shreekumar3d/jigita/demo/wip/smd/tssop20-breakout/scan-helper.FCStd

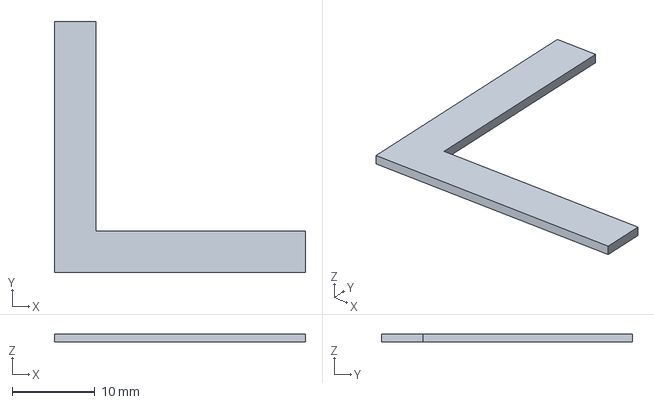
[picture p30: CAD file, 2025-02-22]
demo/wip/smd/tssop20-breakout/scan-helper.FCStd
30.4 x 30.4 x 1.00 mm
