shreekumar3d/jigita/test-boards/component-orientation-test/3dmodels/ssd1306-yrot135.step

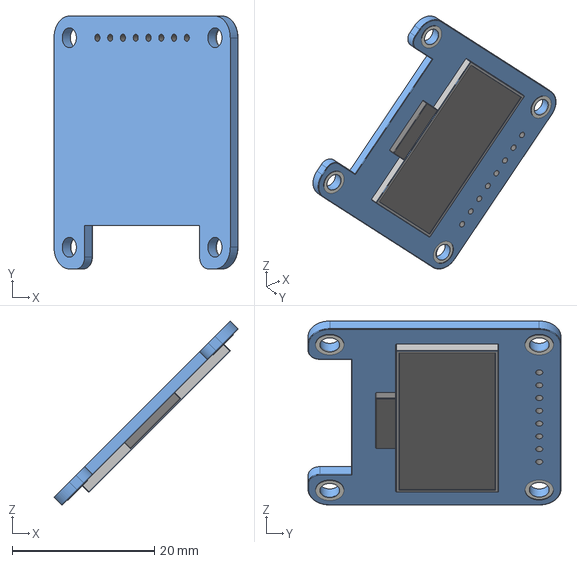
[picture p31: CAD file, 2024-11-05]
test-boards/component-orientation-test/3dmodels/ssd1306-yrot135.step
25.9 x 35.6 x 25.9 mm
