shreekumar3d/jigita/test-boards/footprint-test/2x20pin_berg_header.stl

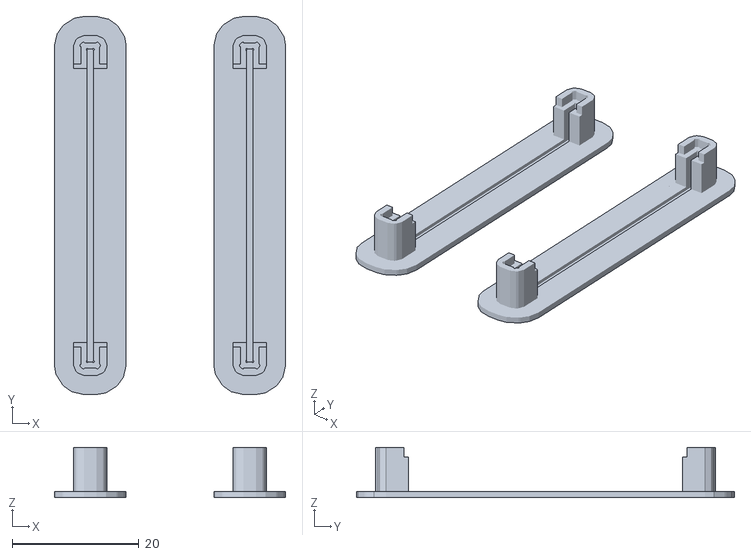
[picture p32: CAD file, 2025-02-27]
test-boards/footprint-test/2x20pin_berg_header.stl
36.5 x 59.6 x 7.94
