shreekumar3d/jigita/test-boards/hello/gen/hello-jig.stl

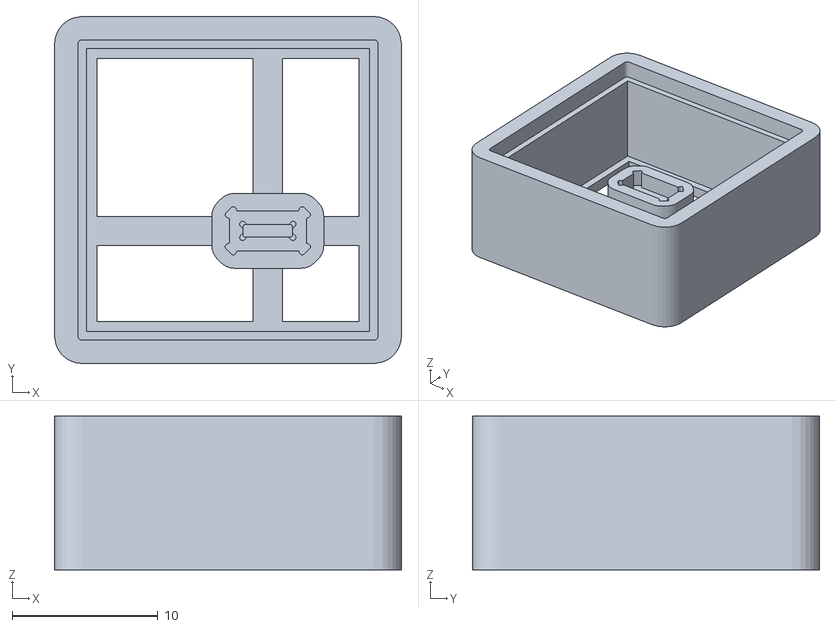
[picture p33: CAD file, 2025-03-18]
test-boards/hello/gen/hello-jig.stl
23.8 x 23.8 x 10.5
