shreekumar3d/jigita/demo/01-rpi-pico-soldering-jig/jigs/pico-soldering-jig.3mf

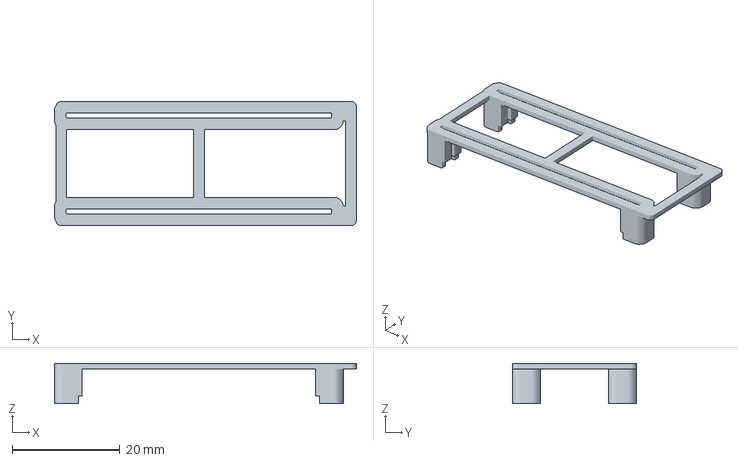
[picture p34: CAD file, 2025-03-20]
demo/01-rpi-pico-soldering-jig/jigs/pico-soldering-jig.3mf
55.9 x 23.0 x 7.44 mm
