shreekumar3d/jigita/demo/03-fossdem-audio-board/jigs/mixolydian-4x4-soldering-jig-solid.3mf

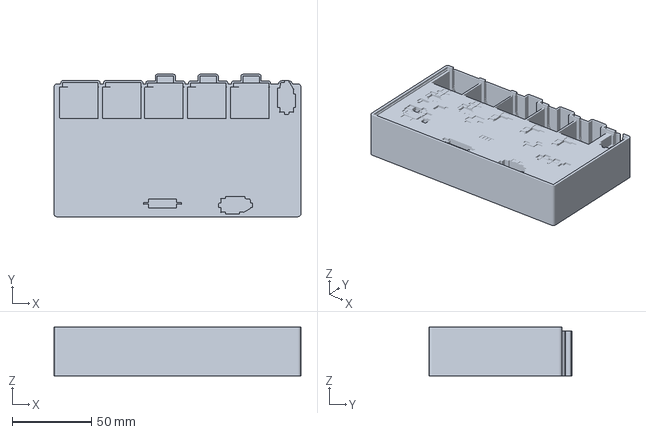
[picture p35: CAD file, 2025-03-24]
demo/03-fossdem-audio-board/jigs/mixolydian-4x4-soldering-jig-solid.3mf
155.8 x 89.9 x 30.8 mm
