shreekumar3d/jigita/demo/04-ativega/jigs/ativega-jig.3mf

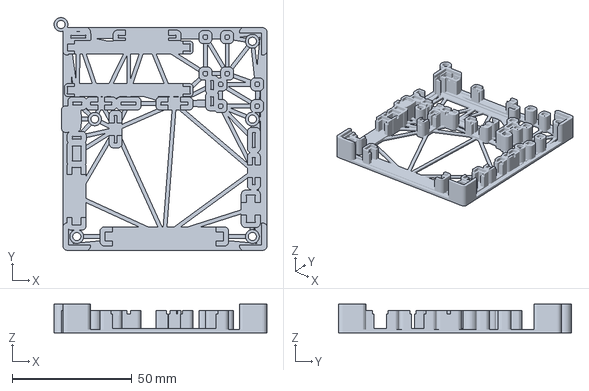
[picture p36: CAD file, 2025-03-26]
demo/04-ativega/jigs/ativega-jig.3mf
88.9 x 97.2 x 11.9 mm
