shreekumar3d/jigita/demo/05-gridfinity/allen-keys/3dmodels/2-HexKey.step

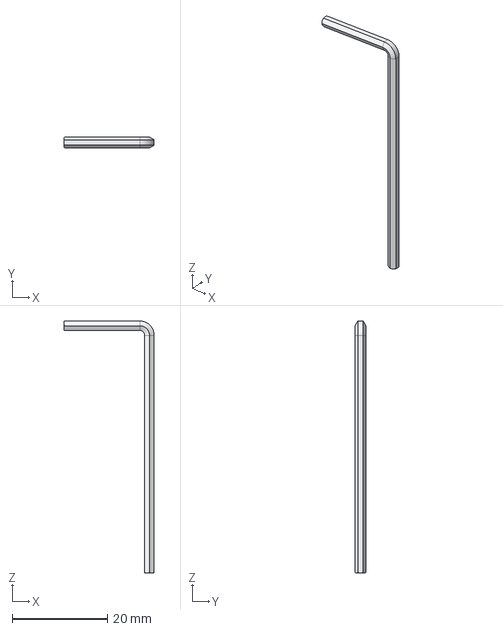
[picture p37: CAD file, 2025-03-27]
demo/05-gridfinity/allen-keys/3dmodels/2-HexKey.step
19.0 x 2.31 x 53.0 mm
