shreekumar3d/jigita/demo/05-gridfinity/base/base-gridfinity-1x1.stl

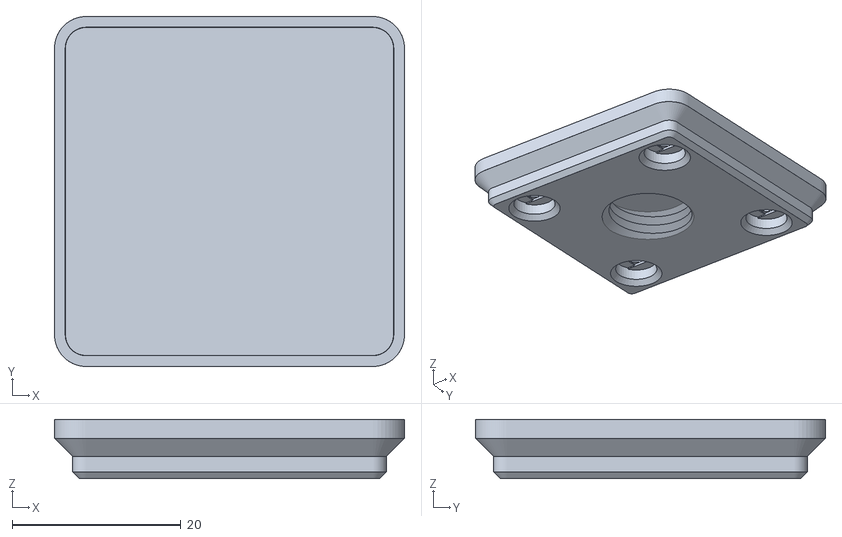
[picture p38: CAD file, 2025-03-26]
demo/05-gridfinity/base/base-gridfinity-1x1.stl
41.5 x 41.5 x 7.00
