shreekumar3d/jigita/demo/05-gridfinity/containers/gridfinity-container-8x10pin-header.stl

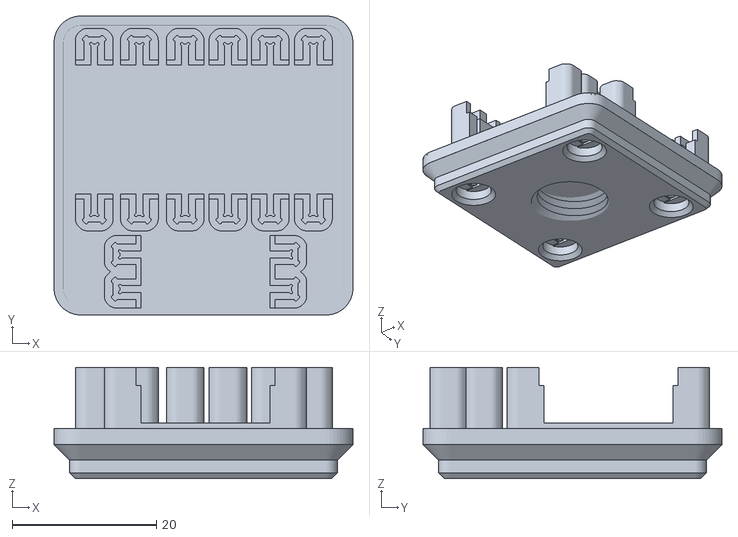
[picture p39: CAD file, 2025-03-26]
demo/05-gridfinity/containers/gridfinity-container-8x10pin-header.stl
41.5 x 41.5 x 15.5
