shreekumar3d/jigita/demo/05-gridfinity/fitting/gridfinity-1x1.FCStd

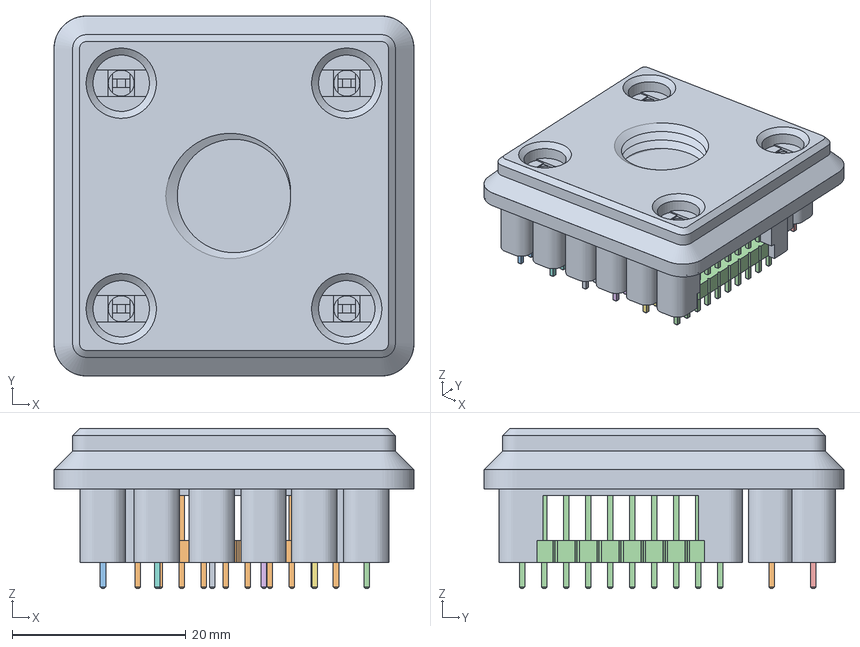
[picture p40: CAD file, 2025-03-26]
demo/05-gridfinity/fitting/gridfinity-1x1.FCStd
41.5 x 41.5 x 18.5 mm
PinHeader_1x10_P254mm_Vertical
PinHeader_1x10_P254mm_Vertical001
PinHeader_1x10_P254mm_Vertical002
PinHeader_1x10_P254mm_Vertical003
PinHeader_1x10_P254mm_Vertical004
PinHeader_1x10_P254mm_Vertical005
PinHeader_1x10_P254mm_Vertical006
PinHeader_1x10_P254mm_Vertical007
gridfinity-container-8x10pin-header
