shreekumar3d/jigita/demo/05-gridfinity/jigs/gridfinity-1x1.3mf

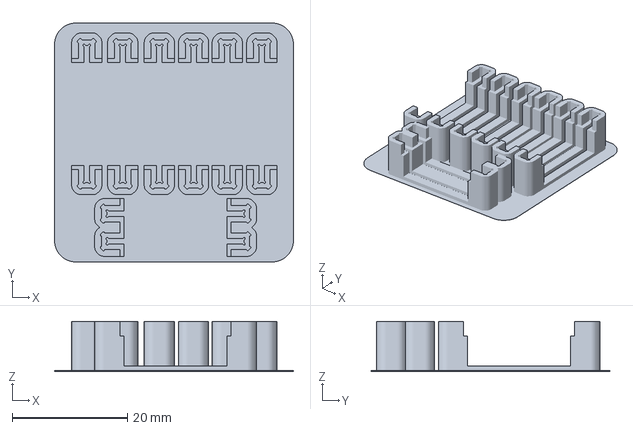
[picture p41: CAD file, 2025-03-26]
demo/05-gridfinity/jigs/gridfinity-1x1.3mf
41.5 x 41.5 x 8.74 mm
