shreekumar3d/jigita/test-boards/component-orientation-test/3dmodels/ssd1306-xrot90.step

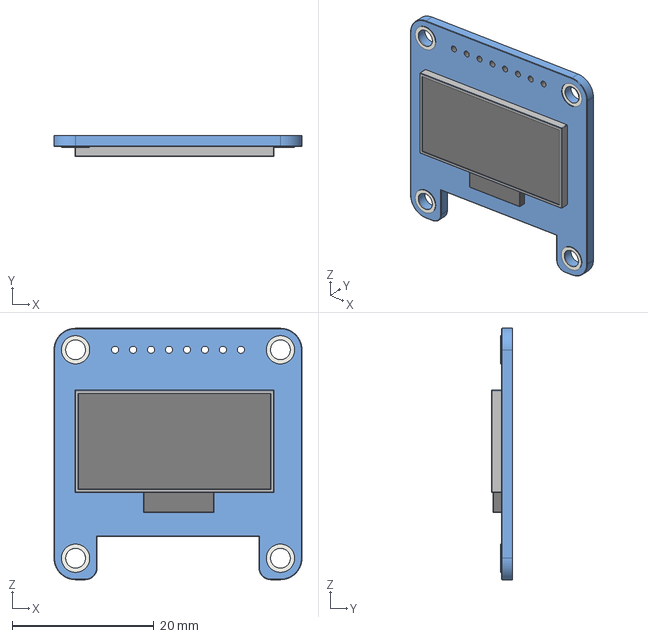
[picture p42: CAD file, 2024-11-05]
test-boards/component-orientation-test/3dmodels/ssd1306-xrot90.step
35.1 x 3.00 x 35.6 mm
