shreekumar3d/jigita/test-boards/hello/gen/hello-kicad.step

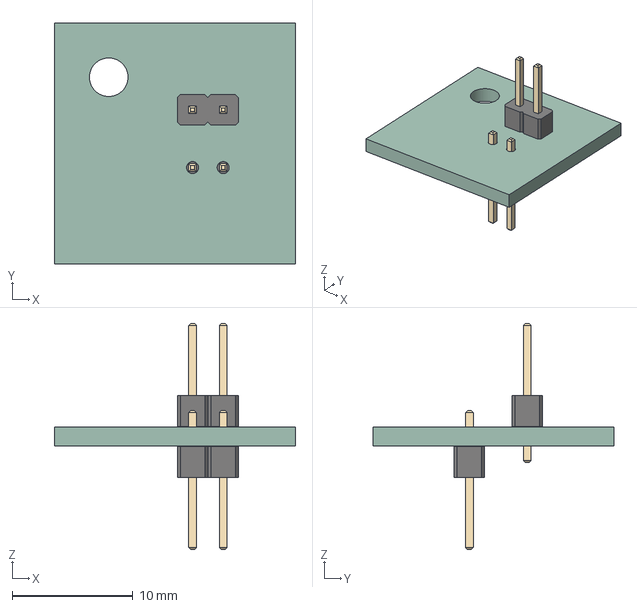
[picture p43: CAD file, 2025-03-18]
test-boards/hello/gen/hello-kicad.step
20.0 x 20.0 x 18.8 mm
PinHeader_1x02_P254mm_Vertical x 2
hello_PCB
