shreekumar3d/jigita/demo/01-rpi-pico-soldering-jig/jigs/pico-all-soldering-jig.3mf

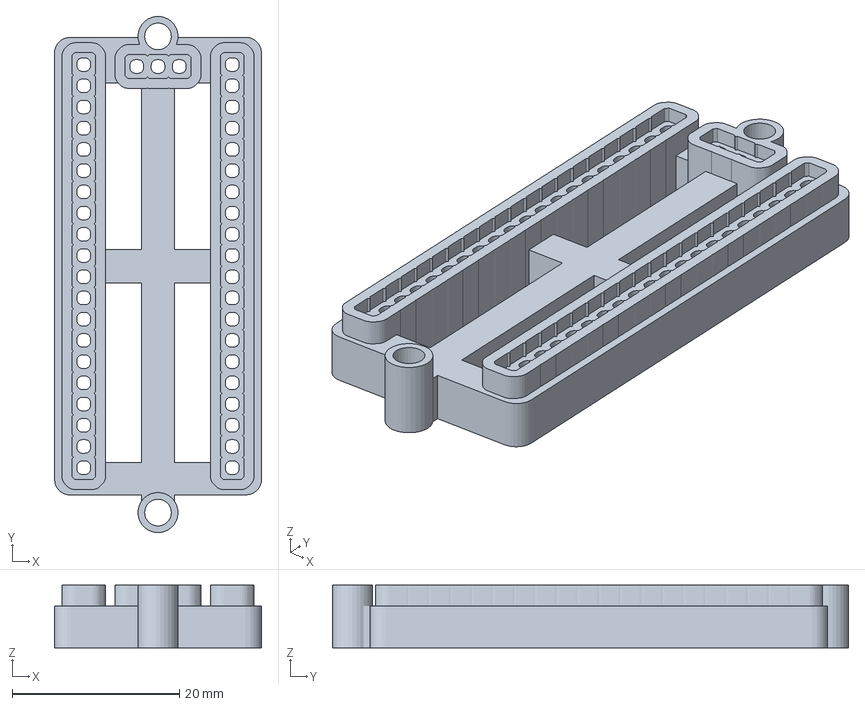
[picture p44: CAD file, 2025-03-20]
demo/01-rpi-pico-soldering-jig/jigs/pico-all-soldering-jig.3mf
24.8 x 61.8 x 7.54 mm
