shreekumar3d/jigita/demo/05-gridfinity/allen-keys/3dmodels/3-HexKey.step

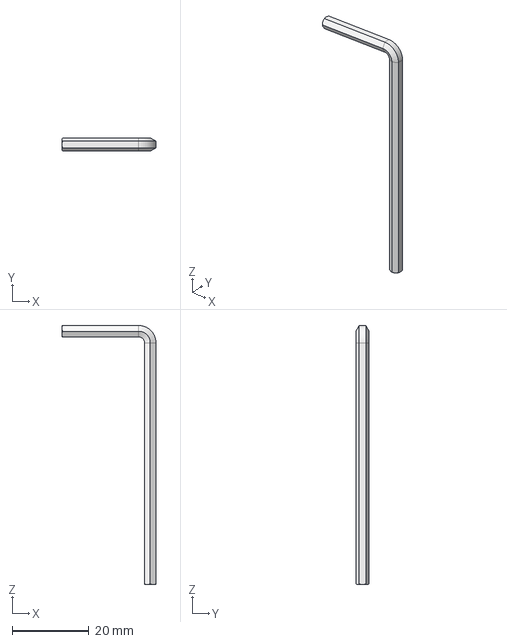
[picture p45: CAD file, 2025-03-27]
demo/05-gridfinity/allen-keys/3dmodels/3-HexKey.step
24.5 x 3.46 x 67.5 mm
