shreekumar3d/jigita/test-boards/component-orientation-test/3dmodels/ssd1306-zrot135.step

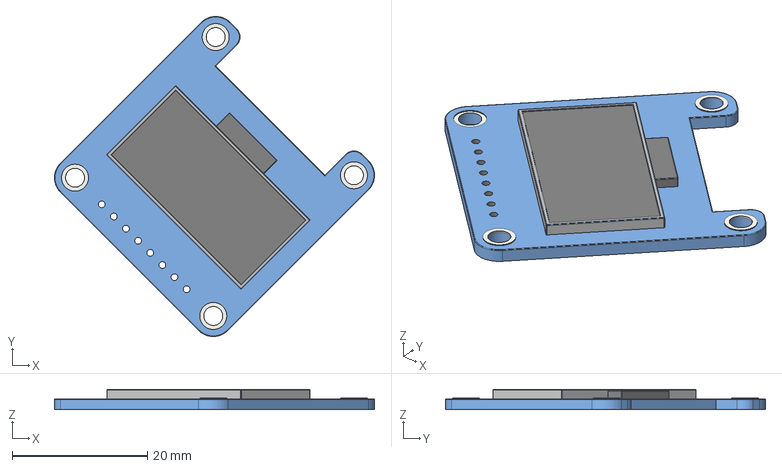
[picture p46: CAD file, 2024-11-05]
test-boards/component-orientation-test/3dmodels/ssd1306-zrot135.step
47.4 x 47.4 x 3.00 mm
