shreekumar3d/jigita/test-boards/hello/gen/hello-jig-on-board.FCStd

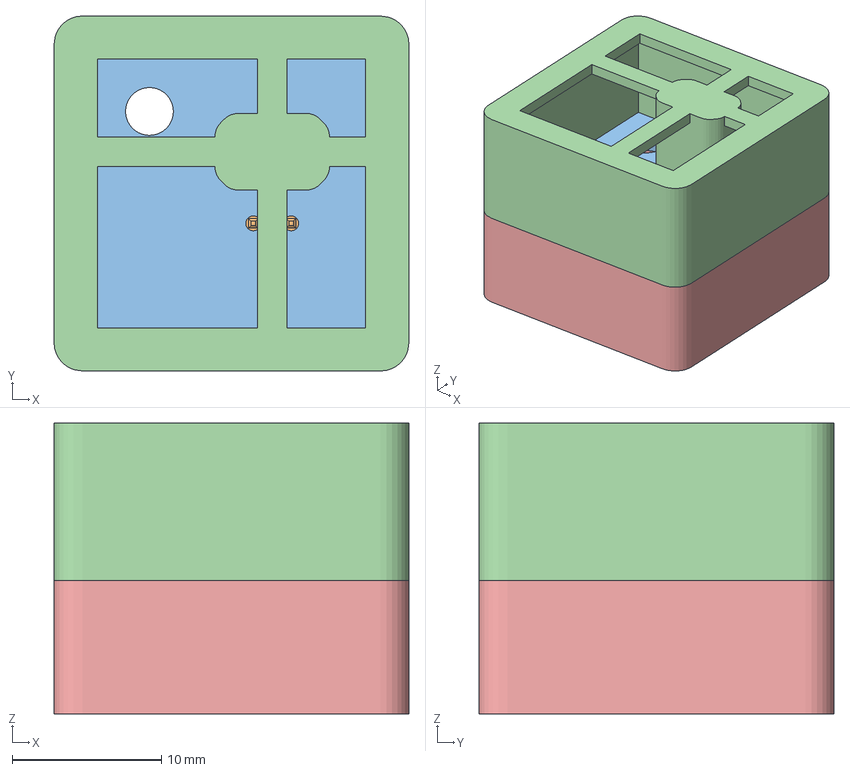
[picture p47: CAD file, 2025-03-18]
test-boards/hello/gen/hello-jig-on-board.FCStd
23.8 x 23.8 x 19.5 mm
PinHeader_1x02_P254mm_Vertical
PinHeader_1x02_P254mm_Vertical001
hello_PCB
hello-jig-step-coord
hello-jig-bottom-step-coord
