shreekumar3d/jigita/test-boards/footprint-test/kicad_single_row_headers.scad

// Customizable Jig Generator
// In OpenSCAD, use "Description Only" for best user experience
// understanding the tunable parameters.
// -----------------------------------------------------
// Auto generated file by jigit, the awesome automatic
// jig generator for your PCB designs. Checkout the project
// at https://github.com/shreekumar3d/jigit
// -----------------------------------------------------
// Configuration file : config.toml
//
// Complete configuration file is embedded at the end of this
// file.
//Thickness(height) of base
Base_Thickness = 0.4; // [0.0:0.2:1.0]
/* [Include these footprints in output STL file] */
//Connector_PinHeader_2.54mm:PinHeader_1x01_P2.54mm_Vertical
Include_FP1_in_Jig=true; // [false,true]
//Connector_PinHeader_2.54mm:PinHeader_1x02_P2.54mm_Vertical
Include_FP2_in_Jig=true; // [false,true]
//Connector_PinHeader_2.54mm:PinHeader_1x03_P2.54mm_Vertical
Include_FP3_in_Jig=true; // [false,true]
//Connector_PinHeader_2.54mm:PinHeader_1x04_P2.54mm_Vertical
Include_FP4_in_Jig=true; // [false,true]
//Connector_PinHeader_2.54mm:PinHeader_1x05_P2.54mm_Vertical
Include_FP5_in_Jig=true; // [false,true]
//Connector_PinHeader_2.54mm:PinHeader_1x06_P2.54mm_Vertical
Include_FP6_in_Jig=true; // [false,true]
//Connector_PinHeader_2.54mm:PinHeader_1x07_P2.54mm_Vertical
Include_FP7_in_Jig=true; // [false,true]
//Connector_PinHeader_2.54mm:PinHeader_1x08_P2.54mm_Vertical
Include_FP8_in_Jig=true; // [false,true]
//Connector_PinHeader_2.54mm:PinHeader_1x09_P2.54mm_Vertical
Include_FP9_in_Jig=true; // [false,true]
/* [Footprint: Connector_PinHeader_2.54mm:PinHeader_1x01_P2.54mm_Vertical] */
//XY Gap in shell for component insertion
Effective_Shell_Gap_For_FP1 = 0.1;
//Thickness of shell
Effective_Shell_Thickness_For_FP1 = 1.2;
//Z distance from start of shell to PCB
Effective_Shell_Clearance_From_PCB_For_FP1 = 1;
//Type of shell for this footprint
Shell_Type_For_FP1="fitting"; // [wiggle,fitting,fitting_flower,tight,courtyard]
//Insert this component into jig from this side.(Bottom insertion requires wiggle or courtyard shell to work)
Insert_FP1_From="top"; // [top,bottom]
//Wrapper thickness
Wrapper_Thickness_For_FP1=0.0; // [0:0.1:10.0]
//Wrapper height
Wrapper_Height_For_FP1=0.0; // [0:0.1:8.539479970932007]
/* [Footprint: Connector_PinHeader_2.54mm:PinHeader_1x02_P2.54mm_Vertical] */
//XY Gap in shell for component insertion
Effective_Shell_Gap_For_FP2 = 0.1;
//Thickness of shell
Effective_Shell_Thickness_For_FP2 = 1.2;
//Z distance from start of shell to PCB
Effective_Shell_Clearance_From_PCB_For_FP2 = 1;
//Type of shell for this footprint
Shell_Type_For_FP2="fitting"; // [wiggle,fitting,fitting_flower,tight,courtyard]
//Insert this component into jig from this side.(Bottom insertion requires wiggle or courtyard shell to work)
Insert_FP2_From="top"; // [top,bottom]
//Wrapper thickness
Wrapper_Thickness_For_FP2=0.0; // [0:0.1:10.0]
//Wrapper height
Wrapper_Height_For_FP2=0.0; // [0:0.1:8.539479970932007]
/* [Footprint: Connector_PinHeader_2.54mm:PinHeader_1x03_P2.54mm_Vertical] */
//XY Gap in shell for component insertion
Effective_Shell_Gap_For_FP3 = 0.1;
//Thickness of shell
Effective_Shell_Thickness_For_FP3 = 1.2;
//Z distance from start of shell to PCB
Effective_Shell_Clearance_From_PCB_For_FP3 = 1;
//Type of shell for this footprint
Shell_Type_For_FP3="fitting"; // [wiggle,fitting,fitting_flower,tight,courtyard]
//Insert this component into jig from this side.(Bottom insertion requires wiggle or courtyard shell to work)
Insert_FP3_From="top"; // [top,bottom]
//Wrapper thickness
Wrapper_Thickness_For_FP3=0.0; // [0:0.1:10.0]
//Wrapper height
Wrapper_Height_For_FP3=0.0; // [0:0.1:8.539479970932007]
/* [Footprint: Connector_PinHeader_2.54mm:PinHeader_1x04_P2.54mm_Vertical] */
//XY Gap in shell for component insertion
Effective_Shell_Gap_For_FP4 = 0.1;
//Thickness of shell
Effective_Shell_Thickness_For_FP4 = 1.2;
//Z distance from start of shell to PCB
Effective_Shell_Clearance_From_PCB_For_FP4 = 1;
//Type of shell for this footprint
Shell_Type_For_FP4="fitting"; // [wiggle,fitting,fitting_flower,tight,courtyard]
//Insert this component into jig from this side.(Bottom insertion requires wiggle or courtyard shell to work)
Insert_FP4_From="top"; // [top,bottom]
//Wrapper thickness
Wrapper_Thickness_For_FP4=0.0; // [0:0.1:10.0]
//Wrapper height
Wrapper_Height_For_FP4=0.0; // [0:0.1:8.539479970932007]
/* [Footprint: Connector_PinHeader_2.54mm:PinHeader_1x05_P2.54mm_Vertical] */
//XY Gap in shell for component insertion
Effective_Shell_Gap_For_FP5 = 0.1;
//Thickness of shell
Effective_Shell_Thickness_For_FP5 = 1.2;
//Z distance from start of shell to PCB
Effective_Shell_Clearance_From_PCB_For_FP5 = 1;
//Type of shell for this footprint
Shell_Type_For_FP5="fitting"; // [wiggle,fitting,fitting_flower,tight,courtyard]
//Insert this component into jig from this side.(Bottom insertion requires wiggle or courtyard shell to work)
Insert_FP5_From="top"; // [top,bottom]
//Wrapper thickness
Wrapper_Thickness_For_FP5=0.0; // [0:0.1:10.0]
//Wrapper height
Wrapper_Height_For_FP5=0.0; // [0:0.1:8.539479970932007]
/* [Footprint: Connector_PinHeader_2.54mm:PinHeader_1x06_P2.54mm_Vertical] */
//XY Gap in shell for component insertion
Effective_Shell_Gap_For_FP6 = 0.1;
//Thickness of shell
Effective_Shell_Thickness_For_FP6 = 1.2;
//Z distance from start of shell to PCB
Effective_Shell_Clearance_From_PCB_For_FP6 = 1;
//Type of shell for this footprint
Shell_Type_For_FP6="fitting"; // [wiggle,fitting,fitting_flower,tight,courtyard]
//Insert this component into jig from this side.(Bottom insertion requires wiggle or courtyard shell to work)
Insert_FP6_From="top"; // [top,bottom]
//Wrapper thickness
Wrapper_Thickness_For_FP6=0.0; // [0:0.1:10.0]
//Wrapper height
Wrapper_Height_For_FP6=0.0; // [0:0.1:8.539479970932007]
/* [Footprint: Connector_PinHeader_2.54mm:PinHeader_1x07_P2.54mm_Vertical] */
//XY Gap in shell for component insertion
Effective_Shell_Gap_For_FP7 = 0.1;
//Thickness of shell
Effective_Shell_Thickness_For_FP7 = 1.2;
//Z distance from start of shell to PCB
Effective_Shell_Clearance_From_PCB_For_FP7 = 1;
//Type of shell for this footprint
Shell_Type_For_FP7="fitting"; // [wiggle,fitting,fitting_flower,tight,courtyard]
//Insert this component into jig from this side.(Bottom insertion requires wiggle or courtyard shell to work)
Insert_FP7_From="top"; // [top,bottom]
//Wrapper thickness
Wrapper_Thickness_For_FP7=0.0; // [0:0.1:10.0]
//Wrapper height
Wrapper_Height_For_FP7=0.0; // [0:0.1:8.539479970932007]
/* [Footprint: Connector_PinHeader_2.54mm:PinHeader_1x08_P2.54mm_Vertical] */
//XY Gap in shell for component insertion
Effective_Shell_Gap_For_FP8 = 0.1;
//Thickness of shell
Effective_Shell_Thickness_For_FP8 = 1.2;
//Z distance from start of shell to PCB
Effective_Shell_Clearance_From_PCB_For_FP8 = 1;
//Type of shell for this footprint
Shell_Type_For_FP8="fitting"; // [wiggle,fitting,fitting_flower,tight,courtyard]
//Insert this component into jig from this side.(Bottom insertion requires wiggle or courtyard shell to work)
Insert_FP8_From="top"; // [top,bottom]
//Wrapper thickness
Wrapper_Thickness_For_FP8=0.0; // [0:0.1:10.0]
//Wrapper height
Wrapper_Height_For_FP8=0.0; // [0:0.1:8.539479970932007]
/* [Footprint: Connector_PinHeader_2.54mm:PinHeader_1x09_P2.54mm_Vertical] */
//XY Gap in shell for component insertion
Effective_Shell_Gap_For_FP9 = 0.1;
//Thickness of shell
Effective_Shell_Thickness_For_FP9 = 1.2;
//Z distance from start of shell to PCB
Effective_Shell_Clearance_From_PCB_For_FP9 = 1;
//Type of shell for this footprint
Shell_Type_For_FP9="fitting"; // [wiggle,fitting,fitting_flower,tight,courtyard]
//Insert this component into jig from this side.(Bottom insertion requires wiggle or courtyard shell to work)
Insert_FP9_From="top"; // [top,bottom]
//Wrapper thickness
Wrapper_Thickness_For_FP9=0.0; // [0:0.1:10.0]
//Wrapper height
Wrapper_Height_For_FP9=0.0; // [0:0.1:8.539479970932007]
/* [Hidden] */

// Height of the tallest component on the top side
topmost_z=8.539479970932007;
    bottom_insertion_z = 9.339479970932008;
// Height of the individual components
max_z_FP1= (Insert_FP1_From=="bottom")? bottom_insertion_z : 8.539479970932007; //Applies to 3D Model(s): ${KICAD8_3DMODEL_DIR}/Connector_PinHeader_2.54mm.3dshapes/PinHeader_1x01_P2.54mm_Vertical.wrl
min_z_FP1= -2.9997399854660034;
max_z_FP2= (Insert_FP2_From=="bottom")? bottom_insertion_z : 8.539479970932007; //Applies to 3D Model(s): ${KICAD8_3DMODEL_DIR}/Connector_PinHeader_2.54mm.3dshapes/PinHeader_1x02_P2.54mm_Vertical.wrl
min_z_FP2= -2.9997399854660034;
max_z_FP3= (Insert_FP3_From=="bottom")? bottom_insertion_z : 8.539479970932007; //Applies to 3D Model(s): ${KICAD8_3DMODEL_DIR}/Connector_PinHeader_2.54mm.3dshapes/PinHeader_1x03_P2.54mm_Vertical.wrl
min_z_FP3= -2.9997399854660034;
max_z_FP4= (Insert_FP4_From=="bottom")? bottom_insertion_z : 8.539479970932007; //Applies to 3D Model(s): ${KICAD8_3DMODEL_DIR}/Connector_PinHeader_2.54mm.3dshapes/PinHeader_1x04_P2.54mm_Vertical.wrl
min_z_FP4= -2.9997399854660034;
max_z_FP5= (Insert_FP5_From=="bottom")? bottom_insertion_z : 8.539479970932007; //Applies to 3D Model(s): ${KICAD8_3DMODEL_DIR}/Connector_PinHeader_2.54mm.3dshapes/PinHeader_1x05_P2.54mm_Vertical.wrl
min_z_FP5= -2.9997399854660034;
max_z_FP6= (Insert_FP6_From=="bottom")? bottom_insertion_z : 8.539479970932007; //Applies to 3D Model(s): ${KICAD8_3DMODEL_DIR}/Connector_PinHeader_2.54mm.3dshapes/PinHeader_1x06_P2.54mm_Vertical.wrl
min_z_FP6= -2.9997399854660034;
max_z_FP7= (Insert_FP7_From=="bottom")? bottom_insertion_z : 8.539479970932007; //Applies to 3D Model(s): ${KICAD8_3DMODEL_DIR}/Connector_PinHeader_2.54mm.3dshapes/PinHeader_1x07_P2.54mm_Vertical.wrl
min_z_FP7= -2.9997399854660034;
max_z_FP8= (Insert_FP8_From=="bottom")? bottom_insertion_z : 8.539479970932007; //Applies to 3D Model(s): ${KICAD8_3DMODEL_DIR}/Connector_PinHeader_2.54mm.3dshapes/PinHeader_1x08_P2.54mm_Vertical.wrl
min_z_FP8= -2.9997399854660034;
max_z_FP9= (Insert_FP9_From=="bottom")? bottom_insertion_z : 8.539479970932007; //Applies to 3D Model(s): ${KICAD8_3DMODEL_DIR}/Connector_PinHeader_2.54mm.3dshapes/PinHeader_1x09_P2.54mm_Vertical.wrl
min_z_FP9= -2.9997399854660034;
// } END : Computed Values

tiny_dimension = 0.0001;
PCB_Thickness = 0;
c_Base_Thickness = Base_Thickness;
c_Base_Line_Height = 1.0;
module peri_line_scad(start,end,line_width){
	hull() {
		translate(v = start) {
			circle(d = line_width);
		}
		translate(v = end) {
			circle(d = line_width);
		}
	}
}
module fitting_cuts_FP1_0(){
	union() {
		translate(v = [0, 0, ((PCB_Thickness - tiny_dimension) + max(2.54, Effective_Shell_Clearance_From_PCB_For_FP1))]) {
			rotate(a = [0, 0, 0]) {
				linear_extrude(height = ((min(((topmost_z + c_Base_Thickness) - c_Base_Line_Height), 8.539479970932007) - max(2.54, Effective_Shell_Clearance_From_PCB_For_FP1)) + (2 * tiny_dimension))) {
					union();
				}
			}
		}
		translate(v = [0, 0, (PCB_Thickness - tiny_dimension)]) {
			rotate(a = [0, 0, 0]) {
				linear_extrude(height = (min(((topmost_z + c_Base_Thickness) - c_Base_Line_Height), 8.539479970932007) + (2 * tiny_dimension))) {
					union();
				}
			}
		}
		translate(v = [0, 0, ((PCB_Thickness - tiny_dimension) + max(-2.9997399854660034, Effective_Shell_Clearance_From_PCB_For_FP1))]) {
			rotate(a = [0, 0, 0]) {
				linear_extrude(height = ((min(((topmost_z + c_Base_Thickness) - c_Base_Line_Height), 2.54) - max(-2.9997399854660034, Effective_Shell_Clearance_From_PCB_For_FP1)) + (2 * tiny_dimension))) {
					union() {
						peri_line_scad([-1.2690761204674887, 1.0156173317072148],[-1.4538520269697461, 1.0921540181802327],0.4);
						hull() {
							union() {
								peri_line_scad([-1.2690761204674887, -1.0156173317072148],[-1.4538520269697461, -1.0921540181802327],0.4);
								peri_line_scad([-1.0156173317072148, -1.2690761204674887],[-1.0921540181802327, -1.4538520269697461],0.4);
							}
						}
						peri_line_scad([-1.0156173317072148, -1.2690761204674887],[-1.0921540181802327, -1.4538520269697461],0.4);
						hull() {
							union() {
								peri_line_scad([1.0156173317072148, -1.2690761204674887],[1.0921540181802327, -1.4538520269697461],0.4);
								peri_line_scad([1.2690761204674887, -1.0156173317072148],[1.4538520269697461, -1.0921540181802327],0.4);
							}
						}
						peri_line_scad([1.2690761204674887, -1.0156173317072148],[1.4538520269697461, -1.0921540181802327],0.4);
						hull() {
							union() {
								peri_line_scad([1.2690761204674887, 1.0156173317072148],[1.4538520269697461, 1.0921540181802327],0.4);
								peri_line_scad([1.0156173317072148, 1.2690761204674887],[1.0921540181802327, 1.4538520269697461],0.4);
							}
						}
						peri_line_scad([1.0156173317072148, 1.2690761204674887],[1.0921540181802327, 1.4538520269697461],0.4);
						hull() {
							union() {
								peri_line_scad([-1.0156173317072148, 1.2690761204674887],[-1.0921540181802327, 1.4538520269697461],0.4);
								peri_line_scad([-1.2690761204674887, 1.0156173317072148],[-1.4538520269697461, 1.0921540181802327],0.4);
							}
						}
					}
				}
			}
		}
		translate(v = [0, 0, (PCB_Thickness - tiny_dimension)]) {
			rotate(a = [0, 0, 0]) {
				linear_extrude(height = (min(((topmost_z + c_Base_Thickness) - c_Base_Line_Height), 2.54) + (2 * tiny_dimension))) {
					union();
				}
			}
		}
	}
}
module hullpoly_FP1_0_0(){
	polygon(points = [[-1.27, 1.0160000151395798], [-1.27, -1.0160000151395798], [-1.0160000151395798, -1.27], [1.0160000151395798, -1.27], [1.27, -1.0160000151395798], [1.27, 1.0160000151395798], [1.0160000151395798, 1.27], [-1.0160000151395798, 1.27]]);
}
module hullpoly_FP1_0_1(){
	polygon(points = [[-0.7200400051474571, -0.32004000514745706], [-0.7200400051474571, 0.32004000514745706], [-0.7181138958163358, 0.3592468612792814], [-0.7123541173087493, 0.3980761339539085], [-0.7028161394403406, 0.43615387604924205], [-0.6895918181519718, 0.473113378093493], [-0.672808510886799, 0.5085986998778562], [-0.6526278500684752, 0.5422680983552979], [-0.6292441864925519, 0.5737973188129153], [-0.6028827176220761, 0.6028827176220761], [-0.5737973188129153, 0.629244186492552], [-0.5422680983552979, 0.6526278500684752], [-0.5085986998778562, 0.6728085108867992], [-0.47311337809349296, 0.6895918181519718], [-0.43615387604924194, 0.7028161394403407], [-0.39807613395390834, 0.7123541173087493], [-0.3592468612792813, 0.7181138958163358], [-0.32004000514745706, 0.7200400051474571], [0.32004000514745706, 0.7200400051474571], [0.3592468612792814, 0.7181138958163358], [0.3980761339539084, 0.7123541173087493], [0.436153876049242, 0.7028161394403407], [0.473113378093493, 0.6895918181519718], [0.5085986998778562, 0.672808510886799], [0.542268098355298, 0.6526278500684752], [0.5737973188129153, 0.6292441864925519], [0.6028827176220761, 0.6028827176220761], [0.6292441864925519, 0.5737973188129153], [0.6526278500684752, 0.5422680983552979], [0.6728085108867992, 0.5085986998778561], [0.6895918181519718, 0.47311337809349296], [0.7028161394403406, 0.436153876049242], [0.7123541173087493, 0.3980761339539084], [0.7181138958163358, 0.3592468612792813], [0.7200400051474571, 0.32004000514745706], [0.7200400051474571, -0.32004000514745706], [0.7181138958163358, -0.35924686127928135], [0.7123541173087493, -0.3980761339539084], [0.7028161394403407, -0.436153876049242], [0.6895918181519718, -0.47311337809349296], [0.672808510886799, -0.5085986998778562], [0.6526278500684752, -0.5422680983552979], [0.6292441864925519, -0.5737973188129153], [0.6028827176220761, -0.6028827176220761], [0.5737973188129153, -0.6292441864925519], [0.542268098355298, -0.6526278500684752], [0.5085986998778562, -0.672808510886799], [0.473113378093493, -0.6895918181519718], [0.436153876049242, -0.7028161394403407], [0.3980761339539084, -0.7123541173087493], [0.3592468612792814, -0.7181138958163358], [0.32004000514745706, -0.7200400051474571], [-0.32004000514745706, -0.7200400051474571], [-0.3592468612792813, -0.7181138958163358], [-0.39807613395390834, -0.7123541173087493], [-0.43615387604924194, -0.7028161394403407], [-0.47311337809349296, -0.6895918181519718], [-0.5085986998778562, -0.6728085108867992], [-0.5422680983552979, -0.6526278500684752], [-0.5737973188129153, -0.629244186492552], [-0.6028827176220761, -0.6028827176220761], [-0.6292441864925519, -0.5737973188129153], [-0.6526278500684752, -0.5422680983552979], [-0.672808510886799, -0.5085986998778562], [-0.6895918181519718, -0.473113378093493], [-0.7028161394403406, -0.43615387604924205], [-0.7123541173087493, -0.3980761339539085], [-0.7181138958163358, -0.3592468612792814], [-0.7200400051474571, -0.32004000514745706]]);
}
module fitting_pocket_FP1_0(){
	union() {
		translate(v = [0, 0, ((PCB_Thickness - tiny_dimension) + -2.9997399854660034)]) {
			rotate(a = [0, 0, 0]) {
				linear_extrude(height = (5.539739985466003 + (2 * tiny_dimension))) {
					offset(r = Effective_Shell_Gap_For_FP1) {
						union() {
							hullpoly_FP1_0_0();
						}
					}
				}
			}
		}
		translate(v = [0, 0, ((PCB_Thickness - tiny_dimension) + 2.54)]) {
			rotate(a = [0, 0, 0]) {
				linear_extrude(height = (5.999479970932007 + (2 * tiny_dimension))) {
					offset(r = Effective_Shell_Gap_For_FP1) {
						union() {
							hullpoly_FP1_0_1();
						}
					}
				}
			}
		}
	}
}
module ref_FP1_0(){
	union() {
		hullpoly_FP1_0_0();
	}
}
module wiggle_pocket_FP1_0(){
	translate(v = [0, 0, (PCB_Thickness + min_z_FP1)]) {
		rotate(a = [0, 0, 0]) {
			linear_extrude(height = (max_z_FP1 - min_z_FP1)) {
				offset(r = Effective_Shell_Gap_For_FP1) {
					union() {
						ref_FP1_0();
					}
				}
			}
		}
	}
}
module perimeter_FP1_0(){
	union() {
		translate(v = [0, 0, (PCB_Thickness + Effective_Shell_Clearance_From_PCB_For_FP1)]) {
			rotate(a = [0, 0, 0]) {
				linear_extrude(height = ((topmost_z - Effective_Shell_Clearance_From_PCB_For_FP1) + c_Base_Thickness)) {
					offset(r = (Effective_Shell_Gap_For_FP1 + Effective_Shell_Thickness_For_FP1)) {
						union() {
							ref_FP1_0();
						}
					}
				}
			}
		}
		translate(v = [0, 0, (((PCB_Thickness + topmost_z) + c_Base_Thickness) - Wrapper_Height_For_FP1)]) {
			rotate(a = [0, 0, 0]) {
				linear_extrude(height = Wrapper_Height_For_FP1) {
					difference() {
						offset(r = ((Effective_Shell_Gap_For_FP1 + Effective_Shell_Thickness_For_FP1) + Wrapper_Thickness_For_FP1)) {
							union() {
								ref_FP1_0();
							}
						}
						offset(r = (Effective_Shell_Gap_For_FP1 + Effective_Shell_Thickness_For_FP1)) {
							union() {
								ref_FP1_0();
							}
						}
					}
				}
			}
		}
	}
}
module fitting_flower_FP1_0(){
	union() {
		translate(v = [0, 0, ((PCB_Thickness + max(-2.9997399854660034, Effective_Shell_Clearance_From_PCB_For_FP1)) - tiny_dimension)]) {
			rotate(a = [0, 0, 0]) {
				linear_extrude(height = ((max_z_FP1 - max(-2.9997399854660034, Effective_Shell_Clearance_From_PCB_For_FP1)) + (2 * tiny_dimension))) {
					difference() {
						offset(r = (Effective_Shell_Gap_For_FP1 + Effective_Shell_Thickness_For_FP1)) {
							union() {
								hullpoly_FP1_0_0();
							}
						}
						offset(r = Effective_Shell_Gap_For_FP1) {
							union() {
								hullpoly_FP1_0_0();
							}
						}
					}
				}
			}
		}
		translate(v = [0, 0, ((PCB_Thickness + max(2.54, Effective_Shell_Clearance_From_PCB_For_FP1)) - tiny_dimension)]) {
			rotate(a = [0, 0, 0]) {
				linear_extrude(height = ((max_z_FP1 - max(2.54, Effective_Shell_Clearance_From_PCB_For_FP1)) + (2 * tiny_dimension))) {
					difference() {
						offset(r = (Effective_Shell_Gap_For_FP1 + Effective_Shell_Thickness_For_FP1)) {
							union() {
								hullpoly_FP1_0_1();
							}
						}
						offset(r = Effective_Shell_Gap_For_FP1) {
							union() {
								hullpoly_FP1_0_1();
							}
						}
					}
				}
			}
		}
		translate(v = [0, 0, (((PCB_Thickness + topmost_z) + c_Base_Thickness) - Wrapper_Height_For_FP1)]) {
			rotate(a = [0, 0, 0]) {
				linear_extrude(height = Wrapper_Height_For_FP1) {
					difference() {
						offset(r = ((Effective_Shell_Gap_For_FP1 + Effective_Shell_Thickness_For_FP1) + Wrapper_Thickness_For_FP1)) {
							union() {
								ref_FP1_0();
							}
						}
						offset(r = (Effective_Shell_Gap_For_FP1 + Effective_Shell_Thickness_For_FP1)) {
							union() {
								ref_FP1_0();
							}
						}
					}
				}
			}
		}
		translate(v = [0, 0, (PCB_Thickness + max_z_FP1)]) {
			rotate(a = [0, 0, 0]) {
				linear_extrude(height = ((topmost_z - max_z_FP1) + c_Base_Thickness)) {
					offset(r = (Effective_Shell_Gap_For_FP1 + Effective_Shell_Thickness_For_FP1)) {
						union() {
							ref_FP1_0();
						}
					}
				}
			}
		}
	}
}
module shape_FP1_0_0(){
	union() {
		polygon(points = [[1.016, -1.27], [1.266, -1.02], [1.27, -1.016], [1.27, 0.984], [1.27, 1.016], [1.02, 1.266], [1.016, 1.27], [-0.984, 1.27], [-1.016, 1.27], [-1.27, 1.016], [-1.27, -1.016], [-1.016, -1.27]]);
	}
}
module keepout_volume_FP1_0_0(){
	translate(v = [0, 0, (PCB_Thickness + max(-2.9997399854660034, Effective_Shell_Clearance_From_PCB_For_FP1))]) {
		rotate(a = [0, 0, 0]) {
			linear_extrude(height = ((2.539479970932007 - max(-2.9997399854660034, Effective_Shell_Clearance_From_PCB_For_FP1)) + tiny_dimension)) {
				offset(r = Effective_Shell_Gap_For_FP1) {
					union() {
						shape_FP1_0_0();
					}
				}
			}
		}
	}
}
module shape_FP1_0_1(){
	union() {
		polygon(points = [[0.209, -0.658], [0.258, -0.65], [0.305, -0.638], [0.351, -0.622], [0.396, -0.601], [0.438, -0.576], [0.477, -0.547], [0.514, -0.514], [0.547, -0.477], [0.576, -0.438], [0.601, -0.396], [0.622, -0.351], [0.638, -0.305], [0.65, -0.258], [0.658, -0.209], [0.66, -0.16], [0.66, 0.16], [0.658, 0.209], [0.65, 0.258], [0.638, 0.305], [0.622, 0.351], [0.601, 0.396], [0.576, 0.438], [0.547, 0.477], [0.514, 0.514], [0.477, 0.547], [0.438, 0.576], [0.396, 0.601], [0.351, 0.622], [0.305, 0.638], [0.258, 0.65], [0.209, 0.658], [0.16, 0.66], [-0.16, 0.66], [-0.209, 0.658], [-0.258, 0.65], [-0.305, 0.638], [-0.351, 0.622], [-0.396, 0.601], [-0.438, 0.576], [-0.477, 0.547], [-0.514, 0.514], [-0.547, 0.477], [-0.576, 0.438], [-0.601, 0.396], [-0.622, 0.351], [-0.638, 0.305], [-0.65, 0.258], [-0.658, 0.209], [-0.66, 0.16], [-0.66, -0.16], [-0.658, -0.209], [-0.65, -0.258], [-0.638, -0.305], [-0.622, -0.351], [-0.601, -0.396], [-0.576, -0.438], [-0.547, -0.477], [-0.514, -0.514], [-0.477, -0.547], [-0.438, -0.576], [-0.396, -0.601], [-0.351, -0.622], [-0.305, -0.638], [-0.258, -0.65], [-0.209, -0.658], [-0.16, -0.66], [0.16, -0.66]]);
	}
}
module keepout_volume_FP1_0_1(){
	translate(v = [0, 0, (PCB_Thickness + max(-2.9997399854660034, Effective_Shell_Clearance_From_PCB_For_FP1))]) {
		rotate(a = [0, 0, 0]) {
			linear_extrude(height = ((8.539479970932007 - max(-2.9997399854660034, Effective_Shell_Clearance_From_PCB_For_FP1)) + tiny_dimension)) {
				offset(r = Effective_Shell_Gap_For_FP1) {
					union() {
						shape_FP1_0_1();
					}
				}
			}
		}
	}
}
module tight_perimeter_FP1_0(){
	union() {
		translate(v = [0, 0, (PCB_Thickness + Effective_Shell_Clearance_From_PCB_For_FP1)]) {
			rotate(a = [0, 0, 0]) {
				linear_extrude(height = ((topmost_z - Effective_Shell_Clearance_From_PCB_For_FP1) + c_Base_Thickness)) {
					offset(r = (Effective_Shell_Gap_For_FP1 + Effective_Shell_Thickness_For_FP1)) {
						union() {
							shape_FP1_0_0();
						}
					}
				}
			}
		}
		translate(v = [0, 0, (((PCB_Thickness + topmost_z) + c_Base_Thickness) - Wrapper_Height_For_FP1)]) {
			rotate(a = [0, 0, 0]) {
				linear_extrude(height = Wrapper_Height_For_FP1) {
					difference() {
						offset(r = ((Effective_Shell_Gap_For_FP1 + Effective_Shell_Thickness_For_FP1) + Wrapper_Thickness_For_FP1)) {
							union() {
								shape_FP1_0_0();
							}
						}
						offset(r = (Effective_Shell_Gap_For_FP1 + Effective_Shell_Thickness_For_FP1)) {
							union() {
								shape_FP1_0_0();
							}
						}
					}
				}
			}
		}
	}
}
module tight_pocket_FP1_0(){
	union() {
		keepout_volume_FP1_0_0();
		keepout_volume_FP1_0_1();
	}
}
module courtyard_FP1(){
	polygon(points = [[1.8, 1.8], [1.8, -1.8], [-1.8, -1.8], [-1.8, 1.8]]);
}
module courtyard_pocket_FP1(){
	translate(v = [0, 0, PCB_Thickness]) {
		translate(v = [0, 0, min_z_FP1]) {
			linear_extrude(height = (max_z_FP1 - min_z_FP1)) {
				offset(r = Effective_Shell_Gap_For_FP1) {
					union() {
						courtyard_FP1();
					}
				}
			}
		}
	}
}
module courtyard_perimeter_FP1(){
	union() {
		translate(v = [0, 0, (PCB_Thickness + Effective_Shell_Clearance_From_PCB_For_FP1)]) {
			linear_extrude(height = ((topmost_z - Effective_Shell_Clearance_From_PCB_For_FP1) + c_Base_Thickness)) {
				offset(r = (Effective_Shell_Gap_For_FP1 + Effective_Shell_Thickness_For_FP1)) {
					union() {
						courtyard_FP1();
					}
				}
			}
		}
		translate(v = [0, 0, (((PCB_Thickness + topmost_z) + c_Base_Thickness) - Wrapper_Height_For_FP1)]) {
			linear_extrude(height = Wrapper_Height_For_FP1) {
				difference() {
					offset(r = ((Effective_Shell_Gap_For_FP1 + Effective_Shell_Thickness_For_FP1) + Wrapper_Thickness_For_FP1)) {
						union() {
							courtyard_FP1();
						}
					}
					offset(r = (Effective_Shell_Gap_For_FP1 + Effective_Shell_Thickness_For_FP1)) {
						union() {
							courtyard_FP1();
						}
					}
				}
			}
		}
	}
}
module fitting_cuts_FP2_0(){
	union() {
		translate(v = [0, 0, ((PCB_Thickness - tiny_dimension) + max(2.54, Effective_Shell_Clearance_From_PCB_For_FP2))]) {
			rotate(a = [0, 0, 0]) {
				linear_extrude(height = ((min(((topmost_z + c_Base_Thickness) - c_Base_Line_Height), 8.539479970932007) - max(2.54, Effective_Shell_Clearance_From_PCB_For_FP2)) + (2 * tiny_dimension))) {
					union() {
						peri_line_scad([0.3193328983662705, -2.8593330119131193],[0.46075425460358, -3.000754368150429],0.4);
						peri_line_scad([0.3193328983662705, 0.3193328983662705],[0.46075425460358, 0.46075425460358],0.4);
						peri_line_scad([-0.3193328983662705, 0.3193328983662705],[-0.46075425460358, 0.46075425460358],0.4);
						peri_line_scad([-0.3193328983662705, -2.8593330119131193],[-0.46075425460358, -3.000754368150429],0.4);
					}
				}
			}
		}
		translate(v = [0, 0, (PCB_Thickness - tiny_dimension)]) {
			rotate(a = [0, 0, 0]) {
				linear_extrude(height = (min(((topmost_z + c_Base_Thickness) - c_Base_Line_Height), 8.539479970932007) + (2 * tiny_dimension))) {
					union();
				}
			}
		}
		translate(v = [0, 0, ((PCB_Thickness - tiny_dimension) + max(-2.9997399854660034, Effective_Shell_Clearance_From_PCB_For_FP2))]) {
			rotate(a = [0, 0, 0]) {
				linear_extrude(height = ((min(((topmost_z + c_Base_Thickness) - c_Base_Line_Height), 2.54) - max(-2.9997399854660034, Effective_Shell_Clearance_From_PCB_For_FP2)) + (2 * tiny_dimension))) {
					union() {
						peri_line_scad([1.2690761204389767, -3.55561725607815],[1.4538520326436606, -3.632153928784291],0.4);
						hull() {
							union() {
								peri_line_scad([1.2690761204674887, 1.0156173317072148],[1.4538520269697461, 1.0921540181802327],0.4);
								peri_line_scad([1.0156173317072148, 1.2690761204674887],[1.0921540181802327, 1.4538520269697461],0.4);
							}
						}
						peri_line_scad([1.0156173317072148, 1.2690761204674887],[1.0921540181802327, 1.4538520269697461],0.4);
						hull() {
							union() {
								peri_line_scad([-1.0156173317072148, 1.2690761204674887],[-1.0921540181802327, 1.4538520269697461],0.4);
								peri_line_scad([-1.2690761204674887, 1.0156173317072148],[-1.4538520269697461, 1.0921540181802327],0.4);
							}
						}
						peri_line_scad([-1.2690761204674887, 1.0156173317072148],[-1.4538520269697461, 1.0921540181802327],0.4);
						hull() {
							union() {
								peri_line_scad([-1.2690761204389767, -3.55561725607815],[-1.4538520326436606, -3.632153928784291],0.4);
								peri_line_scad([-1.0156173316383803, -3.809076120496001],[-1.0921540318782748, -3.993852021295831],0.4);
							}
						}
						peri_line_scad([-1.0156173316383803, -3.809076120496001],[-1.0921540318782748, -3.993852021295831],0.4);
						hull() {
							union() {
								peri_line_scad([1.0156173316383803, -3.809076120496001],[1.0921540318782748, -3.993852021295831],0.4);
								peri_line_scad([1.2690761204389767, -3.55561725607815],[1.4538520326436606, -3.632153928784291],0.4);
							}
						}
					}
				}
			}
		}
		translate(v = [0, 0, (PCB_Thickness - tiny_dimension)]) {
			rotate(a = [0, 0, 0]) {
				linear_extrude(height = (min(((topmost_z + c_Base_Thickness) - c_Base_Line_Height), 2.54) + (2 * tiny_dimension))) {
					union();
				}
			}
		}
	}
}
module hullpoly_FP2_0_0(){
	polygon(points = [[1.27, -3.555999939441681], [1.27, 1.0160000151395798], [1.0160000151395798, 1.27], [-1.0160000151395798, 1.27], [-1.27, 1.0160000151395798], [-1.27, -3.555999939441681], [-1.0160000151395798, -3.81], [1.0160000151395798, -3.81]]);
}
module hullpoly_FP2_0_1(){
	polygon(points = [[0.32004000514745706, -2.8600401186943056], [0.32004000514745706, 0.32004000514745706], [-0.32004000514745706, 0.32004000514745706], [-0.32004000514745706, -2.8600401186943056]]);
}
module fitting_pocket_FP2_0(){
	union() {
		translate(v = [0, 0, ((PCB_Thickness - tiny_dimension) + -2.9997399854660034)]) {
			rotate(a = [0, 0, 0]) {
				linear_extrude(height = (5.539739985466003 + (2 * tiny_dimension))) {
					offset(r = Effective_Shell_Gap_For_FP2) {
						union() {
							hullpoly_FP2_0_0();
						}
					}
				}
			}
		}
		translate(v = [0, 0, ((PCB_Thickness - tiny_dimension) + 2.54)]) {
			rotate(a = [0, 0, 0]) {
				linear_extrude(height = (5.999479970932007 + (2 * tiny_dimension))) {
					offset(r = Effective_Shell_Gap_For_FP2) {
						union() {
							hullpoly_FP2_0_1();
						}
					}
				}
			}
		}
	}
}
module ref_FP2_0(){
	union() {
		hullpoly_FP2_0_0();
	}
}
module wiggle_pocket_FP2_0(){
	translate(v = [0, 0, (PCB_Thickness + min_z_FP2)]) {
		rotate(a = [0, 0, 0]) {
			linear_extrude(height = (max_z_FP2 - min_z_FP2)) {
				offset(r = Effective_Shell_Gap_For_FP2) {
					union() {
						ref_FP2_0();
					}
				}
			}
		}
	}
}
module perimeter_FP2_0(){
	union() {
		translate(v = [0, 0, (PCB_Thickness + Effective_Shell_Clearance_From_PCB_For_FP2)]) {
			rotate(a = [0, 0, 0]) {
				linear_extrude(height = ((topmost_z - Effective_Shell_Clearance_From_PCB_For_FP2) + c_Base_Thickness)) {
					offset(r = (Effective_Shell_Gap_For_FP2 + Effective_Shell_Thickness_For_FP2)) {
						union() {
							ref_FP2_0();
						}
					}
				}
			}
		}
		translate(v = [0, 0, (((PCB_Thickness + topmost_z) + c_Base_Thickness) - Wrapper_Height_For_FP2)]) {
			rotate(a = [0, 0, 0]) {
				linear_extrude(height = Wrapper_Height_For_FP2) {
					difference() {
						offset(r = ((Effective_Shell_Gap_For_FP2 + Effective_Shell_Thickness_For_FP2) + Wrapper_Thickness_For_FP2)) {
							union() {
								ref_FP2_0();
							}
						}
						offset(r = (Effective_Shell_Gap_For_FP2 + Effective_Shell_Thickness_For_FP2)) {
							union() {
								ref_FP2_0();
							}
						}
					}
				}
			}
		}
	}
}
module fitting_flower_FP2_0(){
	union() {
		translate(v = [0, 0, ((PCB_Thickness + max(-2.9997399854660034, Effective_Shell_Clearance_From_PCB_For_FP2)) - tiny_dimension)]) {
			rotate(a = [0, 0, 0]) {
				linear_extrude(height = ((max_z_FP2 - max(-2.9997399854660034, Effective_Shell_Clearance_From_PCB_For_FP2)) + (2 * tiny_dimension))) {
					difference() {
						offset(r = (Effective_Shell_Gap_For_FP2 + Effective_Shell_Thickness_For_FP2)) {
							union() {
								hullpoly_FP2_0_0();
							}
						}
						offset(r = Effective_Shell_Gap_For_FP2) {
							union() {
								hullpoly_FP2_0_0();
							}
						}
					}
				}
			}
		}
		translate(v = [0, 0, ((PCB_Thickness + max(2.54, Effective_Shell_Clearance_From_PCB_For_FP2)) - tiny_dimension)]) {
			rotate(a = [0, 0, 0]) {
				linear_extrude(height = ((max_z_FP2 - max(2.54, Effective_Shell_Clearance_From_PCB_For_FP2)) + (2 * tiny_dimension))) {
					difference() {
						offset(r = (Effective_Shell_Gap_For_FP2 + Effective_Shell_Thickness_For_FP2)) {
							union() {
								hullpoly_FP2_0_1();
							}
						}
						offset(r = Effective_Shell_Gap_For_FP2) {
							union() {
								hullpoly_FP2_0_1();
							}
						}
					}
				}
			}
		}
		translate(v = [0, 0, (((PCB_Thickness + topmost_z) + c_Base_Thickness) - Wrapper_Height_For_FP2)]) {
			rotate(a = [0, 0, 0]) {
				linear_extrude(height = Wrapper_Height_For_FP2) {
					difference() {
						offset(r = ((Effective_Shell_Gap_For_FP2 + Effective_Shell_Thickness_For_FP2) + Wrapper_Thickness_For_FP2)) {
							union() {
								ref_FP2_0();
							}
						}
						offset(r = (Effective_Shell_Gap_For_FP2 + Effective_Shell_Thickness_For_FP2)) {
							union() {
								ref_FP2_0();
							}
						}
					}
				}
			}
		}
		translate(v = [0, 0, (PCB_Thickness + max_z_FP2)]) {
			rotate(a = [0, 0, 0]) {
				linear_extrude(height = ((topmost_z - max_z_FP2) + c_Base_Thickness)) {
					offset(r = (Effective_Shell_Gap_For_FP2 + Effective_Shell_Thickness_For_FP2)) {
						union() {
							ref_FP2_0();
						}
					}
				}
			}
		}
	}
}
module shape_FP2_0_0(){
	union() {
		polygon(points = [[1.016, -3.81], [1.266, -3.56], [1.27, -3.556], [1.27, -1.556], [1.27, -1.524], [1.02, -1.274], [1.016, -1.27], [1.266, -1.02], [1.27, -1.016], [1.27, 0.984], [1.27, 1.016], [1.02, 1.266], [1.016, 1.27], [-0.984, 1.27], [-1.016, 1.27], [-1.27, 1.016], [-1.27, -1.016], [-1.016, -1.27], [-1.27, -1.524], [-1.27, -3.556], [-1.016, -3.81]]);
	}
}
module keepout_volume_FP2_0_0(){
	translate(v = [0, 0, (PCB_Thickness + max(-2.9997399854660034, Effective_Shell_Clearance_From_PCB_For_FP2))]) {
		rotate(a = [0, 0, 0]) {
			linear_extrude(height = ((2.539479970932007 - max(-2.9997399854660034, Effective_Shell_Clearance_From_PCB_For_FP2)) + tiny_dimension)) {
				offset(r = Effective_Shell_Gap_For_FP2) {
					union() {
						shape_FP2_0_0();
					}
				}
			}
		}
	}
}
module shape_FP2_0_1(){
	union() {
		polygon(points = [[0.209, -0.658], [0.258, -0.65], [0.305, -0.638], [0.351, -0.622], [0.396, -0.601], [0.438, -0.576], [0.477, -0.547], [0.514, -0.514], [0.547, -0.477], [0.576, -0.438], [0.601, -0.396], [0.622, -0.351], [0.638, -0.305], [0.65, -0.258], [0.658, -0.209], [0.66, -0.16], [0.66, 0.16], [0.658, 0.209], [0.65, 0.258], [0.638, 0.305], [0.622, 0.351], [0.601, 0.396], [0.576, 0.438], [0.547, 0.477], [0.514, 0.514], [0.477, 0.547], [0.438, 0.576], [0.396, 0.601], [0.351, 0.622], [0.305, 0.638], [0.258, 0.65], [0.209, 0.658], [0.16, 0.66], [-0.16, 0.66], [-0.209, 0.658], [-0.258, 0.65], [-0.305, 0.638], [-0.351, 0.622], [-0.396, 0.601], [-0.438, 0.576], [-0.477, 0.547], [-0.514, 0.514], [-0.547, 0.477], [-0.576, 0.438], [-0.601, 0.396], [-0.622, 0.351], [-0.638, 0.305], [-0.65, 0.258], [-0.658, 0.209], [-0.66, 0.16], [-0.66, -0.16], [-0.658, -0.209], [-0.65, -0.258], [-0.638, -0.305], [-0.622, -0.351], [-0.601, -0.396], [-0.576, -0.438], [-0.547, -0.477], [-0.514, -0.514], [-0.477, -0.547], [-0.438, -0.576], [-0.396, -0.601], [-0.351, -0.622], [-0.305, -0.638], [-0.258, -0.65], [-0.209, -0.658], [-0.16, -0.66], [0.16, -0.66]]);
		polygon(points = [[0.209, -3.198], [0.258, -3.19], [0.305, -3.178], [0.351, -3.162], [0.396, -3.141], [0.438, -3.116], [0.477, -3.087], [0.514, -3.054], [0.547, -3.017], [0.576, -2.978], [0.601, -2.936], [0.622, -2.891], [0.638, -2.845], [0.65, -2.798], [0.658, -2.749], [0.66, -2.7], [0.66, -2.38], [0.658, -2.331], [0.65, -2.282], [0.638, -2.235], [0.622, -2.189], [0.601, -2.144], [0.576, -2.102], [0.547, -2.063], [0.514, -2.026], [0.477, -1.993], [0.438, -1.964], [0.396, -1.939], [0.351, -1.918], [0.305, -1.902], [0.258, -1.89], [0.209, -1.882], [0.16, -1.88], [-0.16, -1.88], [-0.209, -1.882], [-0.258, -1.89], [-0.305, -1.902], [-0.351, -1.918], [-0.396, -1.939], [-0.438, -1.964], [-0.477, -1.993], [-0.514, -2.026], [-0.547, -2.063], [-0.576, -2.102], [-0.601, -2.144], [-0.622, -2.189], [-0.638, -2.235], [-0.65, -2.282], [-0.658, -2.331], [-0.66, -2.38], [-0.66, -2.7], [-0.658, -2.749], [-0.65, -2.798], [-0.638, -2.845], [-0.622, -2.891], [-0.601, -2.936], [-0.576, -2.978], [-0.547, -3.017], [-0.514, -3.054], [-0.477, -3.087], [-0.438, -3.116], [-0.396, -3.141], [-0.351, -3.162], [-0.305, -3.178], [-0.258, -3.19], [-0.209, -3.198], [-0.16, -3.2], [0.16, -3.2]]);
	}
}
module keepout_volume_FP2_0_1(){
	translate(v = [0, 0, (PCB_Thickness + max(-2.9997399854660034, Effective_Shell_Clearance_From_PCB_For_FP2))]) {
		rotate(a = [0, 0, 0]) {
			linear_extrude(height = ((8.539479970932007 - max(-2.9997399854660034, Effective_Shell_Clearance_From_PCB_For_FP2)) + tiny_dimension)) {
				offset(r = Effective_Shell_Gap_For_FP2) {
					union() {
						shape_FP2_0_1();
					}
				}
			}
		}
	}
}
module tight_perimeter_FP2_0(){
	union() {
		translate(v = [0, 0, (PCB_Thickness + Effective_Shell_Clearance_From_PCB_For_FP2)]) {
			rotate(a = [0, 0, 0]) {
				linear_extrude(height = ((topmost_z - Effective_Shell_Clearance_From_PCB_For_FP2) + c_Base_Thickness)) {
					offset(r = (Effective_Shell_Gap_For_FP2 + Effective_Shell_Thickness_For_FP2)) {
						union() {
							shape_FP2_0_0();
						}
					}
				}
			}
		}
		translate(v = [0, 0, (((PCB_Thickness + topmost_z) + c_Base_Thickness) - Wrapper_Height_For_FP2)]) {
			rotate(a = [0, 0, 0]) {
				linear_extrude(height = Wrapper_Height_For_FP2) {
					difference() {
						offset(r = ((Effective_Shell_Gap_For_FP2 + Effective_Shell_Thickness_For_FP2) + Wrapper_Thickness_For_FP2)) {
							union() {
								shape_FP2_0_0();
							}
						}
						offset(r = (Effective_Shell_Gap_For_FP2 + Effective_Shell_Thickness_For_FP2)) {
							union() {
								shape_FP2_0_0();
							}
						}
					}
				}
			}
		}
	}
}
module tight_pocket_FP2_0(){
	union() {
		keepout_volume_FP2_0_0();
		keepout_volume_FP2_0_1();
	}
}
module courtyard_FP2(){
	polygon(points = [[1.8, 4.35], [1.8, -1.8], [-1.8, -1.8], [-1.8, 4.35]]);
}
module courtyard_pocket_FP2(){
	translate(v = [0, 0, PCB_Thickness]) {
		translate(v = [0, 0, min_z_FP2]) {
			linear_extrude(height = (max_z_FP2 - min_z_FP2)) {
				offset(r = Effective_Shell_Gap_For_FP2) {
					union() {
						courtyard_FP2();
					}
				}
			}
		}
	}
}
module courtyard_perimeter_FP2(){
	union() {
		translate(v = [0, 0, (PCB_Thickness + Effective_Shell_Clearance_From_PCB_For_FP2)]) {
			linear_extrude(height = ((topmost_z - Effective_Shell_Clearance_From_PCB_For_FP2) + c_Base_Thickness)) {
				offset(r = (Effective_Shell_Gap_For_FP2 + Effective_Shell_Thickness_For_FP2)) {
					union() {
						courtyard_FP2();
					}
				}
			}
		}
		translate(v = [0, 0, (((PCB_Thickness + topmost_z) + c_Base_Thickness) - Wrapper_Height_For_FP2)]) {
			linear_extrude(height = Wrapper_Height_For_FP2) {
				difference() {
					offset(r = ((Effective_Shell_Gap_For_FP2 + Effective_Shell_Thickness_For_FP2) + Wrapper_Thickness_For_FP2)) {
						union() {
							courtyard_FP2();
						}
					}
					offset(r = (Effective_Shell_Gap_For_FP2 + Effective_Shell_Thickness_For_FP2)) {
						union() {
							courtyard_FP2();
						}
					}
				}
			}
		}
	}
}
module fitting_cuts_FP3_0(){
	union() {
		translate(v = [0, 0, ((PCB_Thickness - tiny_dimension) + max(2.54, Effective_Shell_Clearance_From_PCB_For_FP3))]) {
			rotate(a = [0, 0, 0]) {
				linear_extrude(height = ((min(((topmost_z + c_Base_Thickness) - c_Base_Line_Height), 8.539479970932007) - max(2.54, Effective_Shell_Clearance_From_PCB_For_FP3)) + (2 * tiny_dimension))) {
					union() {
						peri_line_scad([-0.3193328983662705, 0.3193328983662705],[-0.46075425460358, 0.46075425460358],0.4);
						peri_line_scad([-0.3193328983662705, -5.3993327091215235],[-0.46075425460358, -5.540754065358833],0.4);
						peri_line_scad([0.3193328983662705, -5.3993327091215235],[0.46075425460358, -5.540754065358833],0.4);
						peri_line_scad([0.3193328983662705, 0.3193328983662705],[0.46075425460358, 0.46075425460358],0.4);
					}
				}
			}
		}
		translate(v = [0, 0, (PCB_Thickness - tiny_dimension)]) {
			rotate(a = [0, 0, 0]) {
				linear_extrude(height = (min(((topmost_z + c_Base_Thickness) - c_Base_Line_Height), 8.539479970932007) + (2 * tiny_dimension))) {
					union();
				}
			}
		}
		translate(v = [0, 0, ((PCB_Thickness - tiny_dimension) + max(-2.9997399854660034, Effective_Shell_Clearance_From_PCB_For_FP3))]) {
			rotate(a = [0, 0, 0]) {
				linear_extrude(height = ((min(((topmost_z + c_Base_Thickness) - c_Base_Line_Height), 2.54) - max(-2.9997399854660034, Effective_Shell_Clearance_From_PCB_For_FP3)) + (2 * tiny_dimension))) {
					union() {
						peri_line_scad([1.2690761205530252, -6.095617558594408],[1.4538520099479868, -6.1721542863680785],0.4);
						hull() {
							union() {
								peri_line_scad([1.2690761204674887, 1.0156173317072148],[1.4538520269697461, 1.0921540181802327],0.4);
								peri_line_scad([1.0156173317072148, 1.2690761204674887],[1.0921540181802327, 1.4538520269697461],0.4);
							}
						}
						peri_line_scad([1.0156173317072148, 1.2690761204674887],[1.0921540181802327, 1.4538520269697461],0.4);
						hull() {
							union() {
								peri_line_scad([-1.0156173317072148, 1.2690761204674887],[-1.0921540181802327, 1.4538520269697461],0.4);
								peri_line_scad([-1.2690761204674887, 1.0156173317072148],[-1.4538520269697461, 1.0921540181802327],0.4);
							}
						}
						peri_line_scad([-1.2690761204674887, 1.0156173317072148],[-1.4538520269697461, 1.0921540181802327],0.4);
						hull() {
							union() {
								peri_line_scad([-1.2690761205530252, -6.095617558594408],[-1.4538520099479868, -6.1721542863680785],0.4);
								peri_line_scad([-1.015617331913718, -6.349076120381952],[-1.0921539770860798, -6.533852043991495],0.4);
							}
						}
						peri_line_scad([-1.015617331913718, -6.349076120381952],[-1.0921539770860798, -6.533852043991495],0.4);
						hull() {
							union() {
								peri_line_scad([1.015617331913718, -6.349076120381952],[1.0921539770860798, -6.533852043991495],0.4);
								peri_line_scad([1.2690761205530252, -6.095617558594408],[1.4538520099479868, -6.1721542863680785],0.4);
							}
						}
					}
				}
			}
		}
		translate(v = [0, 0, (PCB_Thickness - tiny_dimension)]) {
			rotate(a = [0, 0, 0]) {
				linear_extrude(height = (min(((topmost_z + c_Base_Thickness) - c_Base_Line_Height), 2.54) + (2 * tiny_dimension))) {
					union() {
						hull() {
							union() {
								peri_line_scad([1.2690000000000001, -3.096000242233276],[(1.2690000000000001 + (((0.01 + Effective_Shell_Thickness_For_FP3) + Effective_Shell_Gap_For_FP3) * 1.0)), (-3.096000242233276 + (((0.01 + Effective_Shell_Thickness_For_FP3) + Effective_Shell_Gap_For_FP3) * 0.0))],0.4);
								peri_line_scad([1.2690000000000001, -1.9839999848604206],[(1.2690000000000001 + (((0.01 + Effective_Shell_Thickness_For_FP3) + Effective_Shell_Gap_For_FP3) * 1.0)), (-1.9839999848604206 + (((0.01 + Effective_Shell_Thickness_For_FP3) + Effective_Shell_Gap_For_FP3) * 0.0))],0.4);
							}
						}
						hull() {
							union() {
								peri_line_scad([-1.2690000000000001, -1.9839999848604202],[(-1.2690000000000001 + (((0.01 + Effective_Shell_Thickness_For_FP3) + Effective_Shell_Gap_For_FP3) * -1.0)), (-1.9839999848604202 + (((0.01 + Effective_Shell_Thickness_For_FP3) + Effective_Shell_Gap_For_FP3) * 0.0))],0.4);
								peri_line_scad([-1.2690000000000001, -3.0960002422332757],[(-1.2690000000000001 + (((0.01 + Effective_Shell_Thickness_For_FP3) + Effective_Shell_Gap_For_FP3) * -1.0)), (-3.0960002422332757 + (((0.01 + Effective_Shell_Thickness_For_FP3) + Effective_Shell_Gap_For_FP3) * 0.0))],0.4);
							}
						}
					}
				}
			}
		}
	}
}
module hullpoly_FP3_0_0(){
	polygon(points = [[1.27, -6.096000242233276], [1.27, 1.0160000151395798], [1.0160000151395798, 1.27], [-1.0160000151395798, 1.27], [-1.27, 1.0160000151395798], [-1.27, -6.096000242233276], [-1.0160000151395798, -6.35], [1.0160000151395798, -6.35]]);
}
module hullpoly_FP3_0_1(){
	polygon(points = [[-0.32004000514745706, 0.32004000514745706], [-0.32004000514745706, -5.40003981590271], [0.32004000514745706, -5.40003981590271], [0.32004000514745706, 0.32004000514745706]]);
}
module fitting_pocket_FP3_0(){
	union() {
		translate(v = [0, 0, ((PCB_Thickness - tiny_dimension) + -2.9997399854660034)]) {
			rotate(a = [0, 0, 0]) {
				linear_extrude(height = (5.539739985466003 + (2 * tiny_dimension))) {
					offset(r = Effective_Shell_Gap_For_FP3) {
						union() {
							hullpoly_FP3_0_0();
						}
					}
				}
			}
		}
		translate(v = [0, 0, ((PCB_Thickness - tiny_dimension) + 2.54)]) {
			rotate(a = [0, 0, 0]) {
				linear_extrude(height = (5.999479970932007 + (2 * tiny_dimension))) {
					offset(r = Effective_Shell_Gap_For_FP3) {
						union() {
							hullpoly_FP3_0_1();
						}
					}
				}
			}
		}
	}
}
module ref_FP3_0(){
	union() {
		hullpoly_FP3_0_0();
	}
}
module wiggle_pocket_FP3_0(){
	translate(v = [0, 0, (PCB_Thickness + min_z_FP3)]) {
		rotate(a = [0, 0, 0]) {
			linear_extrude(height = (max_z_FP3 - min_z_FP3)) {
				offset(r = Effective_Shell_Gap_For_FP3) {
					union() {
						ref_FP3_0();
					}
				}
			}
		}
	}
}
module perimeter_FP3_0(){
	union() {
		translate(v = [0, 0, (PCB_Thickness + Effective_Shell_Clearance_From_PCB_For_FP3)]) {
			rotate(a = [0, 0, 0]) {
				linear_extrude(height = ((topmost_z - Effective_Shell_Clearance_From_PCB_For_FP3) + c_Base_Thickness)) {
					offset(r = (Effective_Shell_Gap_For_FP3 + Effective_Shell_Thickness_For_FP3)) {
						union() {
							ref_FP3_0();
						}
					}
				}
			}
		}
		translate(v = [0, 0, (((PCB_Thickness + topmost_z) + c_Base_Thickness) - Wrapper_Height_For_FP3)]) {
			rotate(a = [0, 0, 0]) {
				linear_extrude(height = Wrapper_Height_For_FP3) {
					difference() {
						offset(r = ((Effective_Shell_Gap_For_FP3 + Effective_Shell_Thickness_For_FP3) + Wrapper_Thickness_For_FP3)) {
							union() {
								ref_FP3_0();
							}
						}
						offset(r = (Effective_Shell_Gap_For_FP3 + Effective_Shell_Thickness_For_FP3)) {
							union() {
								ref_FP3_0();
							}
						}
					}
				}
			}
		}
	}
}
module fitting_flower_FP3_0(){
	union() {
		translate(v = [0, 0, ((PCB_Thickness + max(-2.9997399854660034, Effective_Shell_Clearance_From_PCB_For_FP3)) - tiny_dimension)]) {
			rotate(a = [0, 0, 0]) {
				linear_extrude(height = ((max_z_FP3 - max(-2.9997399854660034, Effective_Shell_Clearance_From_PCB_For_FP3)) + (2 * tiny_dimension))) {
					difference() {
						offset(r = (Effective_Shell_Gap_For_FP3 + Effective_Shell_Thickness_For_FP3)) {
							union() {
								hullpoly_FP3_0_0();
							}
						}
						offset(r = Effective_Shell_Gap_For_FP3) {
							union() {
								hullpoly_FP3_0_0();
							}
						}
					}
				}
			}
		}
		translate(v = [0, 0, ((PCB_Thickness + max(2.54, Effective_Shell_Clearance_From_PCB_For_FP3)) - tiny_dimension)]) {
			rotate(a = [0, 0, 0]) {
				linear_extrude(height = ((max_z_FP3 - max(2.54, Effective_Shell_Clearance_From_PCB_For_FP3)) + (2 * tiny_dimension))) {
					difference() {
						offset(r = (Effective_Shell_Gap_For_FP3 + Effective_Shell_Thickness_For_FP3)) {
							union() {
								hullpoly_FP3_0_1();
							}
						}
						offset(r = Effective_Shell_Gap_For_FP3) {
							union() {
								hullpoly_FP3_0_1();
							}
						}
					}
				}
			}
		}
		translate(v = [0, 0, (((PCB_Thickness + topmost_z) + c_Base_Thickness) - Wrapper_Height_For_FP3)]) {
			rotate(a = [0, 0, 0]) {
				linear_extrude(height = Wrapper_Height_For_FP3) {
					difference() {
						offset(r = ((Effective_Shell_Gap_For_FP3 + Effective_Shell_Thickness_For_FP3) + Wrapper_Thickness_For_FP3)) {
							union() {
								ref_FP3_0();
							}
						}
						offset(r = (Effective_Shell_Gap_For_FP3 + Effective_Shell_Thickness_For_FP3)) {
							union() {
								ref_FP3_0();
							}
						}
					}
				}
			}
		}
		translate(v = [0, 0, (PCB_Thickness + max_z_FP3)]) {
			rotate(a = [0, 0, 0]) {
				linear_extrude(height = ((topmost_z - max_z_FP3) + c_Base_Thickness)) {
					offset(r = (Effective_Shell_Gap_For_FP3 + Effective_Shell_Thickness_For_FP3)) {
						union() {
							ref_FP3_0();
						}
					}
				}
			}
		}
	}
}
module shape_FP3_0_0(){
	union() {
		polygon(points = [[1.016, -6.35], [1.266, -6.1], [1.27, -6.096], [1.27, -4.096], [1.27, -4.064], [1.02, -3.814], [1.016, -3.81], [1.266, -3.56], [1.27, -3.556], [1.27, -1.556], [1.27, -1.524], [1.02, -1.274], [1.016, -1.27], [1.266, -1.02], [1.27, -1.016], [1.27, 0.984], [1.27, 1.016], [1.02, 1.266], [1.016, 1.27], [-0.984, 1.27], [-1.016, 1.27], [-1.27, 1.016], [-1.27, -1.016], [-1.016, -1.27], [-1.27, -1.524], [-1.27, -3.556], [-1.016, -3.81], [-1.27, -4.064], [-1.27, -6.096], [-1.016, -6.35]]);
	}
}
module keepout_volume_FP3_0_0(){
	translate(v = [0, 0, (PCB_Thickness + max(-2.9997399854660034, Effective_Shell_Clearance_From_PCB_For_FP3))]) {
		rotate(a = [0, 0, 0]) {
			linear_extrude(height = ((2.539479970932007 - max(-2.9997399854660034, Effective_Shell_Clearance_From_PCB_For_FP3)) + tiny_dimension)) {
				offset(r = Effective_Shell_Gap_For_FP3) {
					union() {
						shape_FP3_0_0();
					}
				}
			}
		}
	}
}
module shape_FP3_0_1(){
	union() {
		polygon(points = [[0.209, -0.658], [0.258, -0.65], [0.305, -0.638], [0.351, -0.622], [0.396, -0.601], [0.438, -0.576], [0.477, -0.547], [0.514, -0.514], [0.547, -0.477], [0.576, -0.438], [0.601, -0.396], [0.622, -0.351], [0.638, -0.305], [0.65, -0.258], [0.658, -0.209], [0.66, -0.16], [0.66, 0.16], [0.658, 0.209], [0.65, 0.258], [0.638, 0.305], [0.622, 0.351], [0.601, 0.396], [0.576, 0.438], [0.547, 0.477], [0.514, 0.514], [0.477, 0.547], [0.438, 0.576], [0.396, 0.601], [0.351, 0.622], [0.305, 0.638], [0.258, 0.65], [0.209, 0.658], [0.16, 0.66], [-0.16, 0.66], [-0.209, 0.658], [-0.258, 0.65], [-0.305, 0.638], [-0.351, 0.622], [-0.396, 0.601], [-0.438, 0.576], [-0.477, 0.547], [-0.514, 0.514], [-0.547, 0.477], [-0.576, 0.438], [-0.601, 0.396], [-0.622, 0.351], [-0.638, 0.305], [-0.65, 0.258], [-0.658, 0.209], [-0.66, 0.16], [-0.66, -0.16], [-0.658, -0.209], [-0.65, -0.258], [-0.638, -0.305], [-0.622, -0.351], [-0.601, -0.396], [-0.576, -0.438], [-0.547, -0.477], [-0.514, -0.514], [-0.477, -0.547], [-0.438, -0.576], [-0.396, -0.601], [-0.351, -0.622], [-0.305, -0.638], [-0.258, -0.65], [-0.209, -0.658], [-0.16, -0.66], [0.16, -0.66]]);
		polygon(points = [[0.209, -3.198], [0.258, -3.19], [0.305, -3.178], [0.351, -3.162], [0.396, -3.141], [0.438, -3.116], [0.477, -3.087], [0.514, -3.054], [0.547, -3.017], [0.576, -2.978], [0.601, -2.936], [0.622, -2.891], [0.638, -2.845], [0.65, -2.798], [0.658, -2.749], [0.66, -2.7], [0.66, -2.38], [0.658, -2.331], [0.65, -2.282], [0.638, -2.235], [0.622, -2.189], [0.601, -2.144], [0.576, -2.102], [0.547, -2.063], [0.514, -2.026], [0.477, -1.993], [0.438, -1.964], [0.396, -1.939], [0.351, -1.918], [0.305, -1.902], [0.258, -1.89], [0.209, -1.882], [0.16, -1.88], [-0.16, -1.88], [-0.209, -1.882], [-0.258, -1.89], [-0.305, -1.902], [-0.351, -1.918], [-0.396, -1.939], [-0.438, -1.964], [-0.477, -1.993], [-0.514, -2.026], [-0.547, -2.063], [-0.576, -2.102], [-0.601, -2.144], [-0.622, -2.189], [-0.638, -2.235], [-0.65, -2.282], [-0.658, -2.331], [-0.66, -2.38], [-0.66, -2.7], [-0.658, -2.749], [-0.65, -2.798], [-0.638, -2.845], [-0.622, -2.891], [-0.601, -2.936], [-0.576, -2.978], [-0.547, -3.017], [-0.514, -3.054], [-0.477, -3.087], [-0.438, -3.116], [-0.396, -3.141], [-0.351, -3.162], [-0.305, -3.178], [-0.258, -3.19], [-0.209, -3.198], [-0.16, -3.2], [0.16, -3.2]]);
		polygon(points = [[0.209, -5.738], [0.258, -5.73], [0.305, -5.718], [0.351, -5.702], [0.396, -5.681], [0.438, -5.656], [0.477, -5.627], [0.514, -5.594], [0.547, -5.557], [0.576, -5.518], [0.601, -5.476], [0.622, -5.431], [0.638, -5.385], [0.65, -5.338], [0.658, -5.289], [0.66, -5.24], [0.66, -4.92], [0.658, -4.871], [0.65, -4.822], [0.638, -4.775], [0.622, -4.729], [0.601, -4.684], [0.576, -4.642], [0.547, -4.603], [0.514, -4.566], [0.477, -4.533], [0.438, -4.504], [0.396, -4.479], [0.351, -4.458], [0.305, -4.442], [0.258, -4.43], [0.209, -4.422], [0.16, -4.42], [-0.16, -4.42], [-0.209, -4.422], [-0.258, -4.43], [-0.305, -4.442], [-0.351, -4.458], [-0.396, -4.479], [-0.438, -4.504], [-0.477, -4.533], [-0.514, -4.566], [-0.547, -4.603], [-0.576, -4.642], [-0.601, -4.684], [-0.622, -4.729], [-0.638, -4.775], [-0.65, -4.822], [-0.658, -4.871], [-0.66, -4.92], [-0.66, -5.24], [-0.658, -5.289], [-0.65, -5.338], [-0.638, -5.385], [-0.622, -5.431], [-0.601, -5.476], [-0.576, -5.518], [-0.547, -5.557], [-0.514, -5.594], [-0.477, -5.627], [-0.438, -5.656], [-0.396, -5.681], [-0.351, -5.702], [-0.305, -5.718], [-0.258, -5.73], [-0.209, -5.738], [-0.16, -5.74], [0.16, -5.74]]);
	}
}
module keepout_volume_FP3_0_1(){
	translate(v = [0, 0, (PCB_Thickness + max(-2.9997399854660034, Effective_Shell_Clearance_From_PCB_For_FP3))]) {
		rotate(a = [0, 0, 0]) {
			linear_extrude(height = ((8.539479970932007 - max(-2.9997399854660034, Effective_Shell_Clearance_From_PCB_For_FP3)) + tiny_dimension)) {
				offset(r = Effective_Shell_Gap_For_FP3) {
					union() {
						shape_FP3_0_1();
					}
				}
			}
		}
	}
}
module tight_perimeter_FP3_0(){
	union() {
		translate(v = [0, 0, (PCB_Thickness + Effective_Shell_Clearance_From_PCB_For_FP3)]) {
			rotate(a = [0, 0, 0]) {
				linear_extrude(height = ((topmost_z - Effective_Shell_Clearance_From_PCB_For_FP3) + c_Base_Thickness)) {
					offset(r = (Effective_Shell_Gap_For_FP3 + Effective_Shell_Thickness_For_FP3)) {
						union() {
							shape_FP3_0_0();
						}
					}
				}
			}
		}
		translate(v = [0, 0, (((PCB_Thickness + topmost_z) + c_Base_Thickness) - Wrapper_Height_For_FP3)]) {
			rotate(a = [0, 0, 0]) {
				linear_extrude(height = Wrapper_Height_For_FP3) {
					difference() {
						offset(r = ((Effective_Shell_Gap_For_FP3 + Effective_Shell_Thickness_For_FP3) + Wrapper_Thickness_For_FP3)) {
							union() {
								shape_FP3_0_0();
							}
						}
						offset(r = (Effective_Shell_Gap_For_FP3 + Effective_Shell_Thickness_For_FP3)) {
							union() {
								shape_FP3_0_0();
							}
						}
					}
				}
			}
		}
	}
}
module tight_pocket_FP3_0(){
	union() {
		keepout_volume_FP3_0_0();
		keepout_volume_FP3_0_1();
	}
}
module courtyard_FP3(){
	polygon(points = [[1.8, 6.85], [1.8, -1.8], [-1.8, -1.8], [-1.8, 6.85]]);
}
module courtyard_pocket_FP3(){
	translate(v = [0, 0, PCB_Thickness]) {
		translate(v = [0, 0, min_z_FP3]) {
			linear_extrude(height = (max_z_FP3 - min_z_FP3)) {
				offset(r = Effective_Shell_Gap_For_FP3) {
					union() {
						courtyard_FP3();
					}
				}
			}
		}
	}
}
module courtyard_perimeter_FP3(){
	union() {
		translate(v = [0, 0, (PCB_Thickness + Effective_Shell_Clearance_From_PCB_For_FP3)]) {
			linear_extrude(height = ((topmost_z - Effective_Shell_Clearance_From_PCB_For_FP3) + c_Base_Thickness)) {
				offset(r = (Effective_Shell_Gap_For_FP3 + Effective_Shell_Thickness_For_FP3)) {
					union() {
						courtyard_FP3();
					}
				}
			}
		}
		translate(v = [0, 0, (((PCB_Thickness + topmost_z) + c_Base_Thickness) - Wrapper_Height_For_FP3)]) {
			linear_extrude(height = Wrapper_Height_For_FP3) {
				difference() {
					offset(r = ((Effective_Shell_Gap_For_FP3 + Effective_Shell_Thickness_For_FP3) + Wrapper_Thickness_For_FP3)) {
						union() {
							courtyard_FP3();
						}
					}
					offset(r = (Effective_Shell_Gap_For_FP3 + Effective_Shell_Thickness_For_FP3)) {
						union() {
							courtyard_FP3();
						}
					}
				}
			}
		}
	}
}
module fitting_cuts_FP4_0(){
	union() {
		translate(v = [0, 0, ((PCB_Thickness - tiny_dimension) + max(2.54, Effective_Shell_Clearance_From_PCB_For_FP4))]) {
			rotate(a = [0, 0, 0]) {
				linear_extrude(height = ((min(((topmost_z + c_Base_Thickness) - c_Base_Line_Height), 8.539479970932007) - max(2.54, Effective_Shell_Clearance_From_PCB_For_FP4)) + (2 * tiny_dimension))) {
					union() {
						peri_line_scad([0.3193328983662705, -7.939332709121524],[0.46075425460358, -8.080754065358834],0.4);
						peri_line_scad([0.3193328983662705, 0.3193328983662705],[0.46075425460358, 0.46075425460358],0.4);
						peri_line_scad([-0.3193328983662705, 0.3193328983662705],[-0.46075425460358, 0.46075425460358],0.4);
						peri_line_scad([-0.3193328983662705, -7.939332709121524],[-0.46075425460358, -8.080754065358834],0.4);
					}
				}
			}
		}
		translate(v = [0, 0, (PCB_Thickness - tiny_dimension)]) {
			rotate(a = [0, 0, 0]) {
				linear_extrude(height = (min(((topmost_z + c_Base_Thickness) - c_Base_Line_Height), 8.539479970932007) + (2 * tiny_dimension))) {
					union() {
						hull() {
							union() {
								peri_line_scad([0.31904000514745706, -4.94003981590271],[(0.31904000514745706 + (((0.9600000000000006 + Effective_Shell_Thickness_For_FP4) + Effective_Shell_Gap_For_FP4) * 1.0)), (-4.94003981590271 + (((0.9600000000000006 + Effective_Shell_Thickness_For_FP4) + Effective_Shell_Gap_For_FP4) * 0.0))],0.4);
								peri_line_scad([0.31904000514745706, -2.6799599948525428],[(0.31904000514745706 + (((0.9600000000000006 + Effective_Shell_Thickness_For_FP4) + Effective_Shell_Gap_For_FP4) * 1.0)), (-2.6799599948525428 + (((0.9600000000000006 + Effective_Shell_Thickness_For_FP4) + Effective_Shell_Gap_For_FP4) * 0.0))],0.4);
							}
						}
						hull() {
							union() {
								peri_line_scad([-0.31904000514745706, -2.6799599948525428],[(-0.31904000514745706 + (((0.9600000000000006 + Effective_Shell_Thickness_For_FP4) + Effective_Shell_Gap_For_FP4) * -1.0)), (-2.6799599948525428 + (((0.9600000000000006 + Effective_Shell_Thickness_For_FP4) + Effective_Shell_Gap_For_FP4) * 0.0))],0.4);
								peri_line_scad([-0.31904000514745706, -4.94003981590271],[(-0.31904000514745706 + (((0.9600000000000006 + Effective_Shell_Thickness_For_FP4) + Effective_Shell_Gap_For_FP4) * -1.0)), (-4.94003981590271 + (((0.9600000000000006 + Effective_Shell_Thickness_For_FP4) + Effective_Shell_Gap_For_FP4) * 0.0))],0.4);
							}
						}
					}
				}
			}
		}
		translate(v = [0, 0, ((PCB_Thickness - tiny_dimension) + max(-2.9997399854660034, Effective_Shell_Clearance_From_PCB_For_FP4))]) {
			rotate(a = [0, 0, 0]) {
				linear_extrude(height = ((min(((topmost_z + c_Base_Thickness) - c_Base_Line_Height), 2.54) - max(-2.9997399854660034, Effective_Shell_Clearance_From_PCB_For_FP4)) + (2 * tiny_dimension))) {
					union() {
						peri_line_scad([1.2690761205530252, -8.635617558594408],[1.4538520099479868, -8.712154286368078],0.4);
						hull() {
							union() {
								peri_line_scad([1.2690761204674887, 1.0156173317072148],[1.4538520269697461, 1.0921540181802327],0.4);
								peri_line_scad([1.0156173317072148, 1.2690761204674887],[1.0921540181802327, 1.4538520269697461],0.4);
							}
						}
						peri_line_scad([1.0156173317072148, 1.2690761204674887],[1.0921540181802327, 1.4538520269697461],0.4);
						hull() {
							union() {
								peri_line_scad([-1.0156173317072148, 1.2690761204674887],[-1.0921540181802327, 1.4538520269697461],0.4);
								peri_line_scad([-1.2690761204674887, 1.0156173317072148],[-1.4538520269697461, 1.0921540181802327],0.4);
							}
						}
						peri_line_scad([-1.2690761204674887, 1.0156173317072148],[-1.4538520269697461, 1.0921540181802327],0.4);
						hull() {
							union() {
								peri_line_scad([-1.2690761205530252, -8.635617558594408],[-1.4538520099479868, -8.712154286368078],0.4);
								peri_line_scad([-1.015617331913718, -8.889076120381953],[-1.0921539770860798, -9.073852043991497],0.4);
							}
						}
						peri_line_scad([-1.015617331913718, -8.889076120381953],[-1.0921539770860798, -9.073852043991497],0.4);
						hull() {
							union() {
								peri_line_scad([1.015617331913718, -8.889076120381953],[1.0921539770860798, -9.073852043991497],0.4);
								peri_line_scad([1.2690761205530252, -8.635617558594408],[1.4538520099479868, -8.712154286368078],0.4);
							}
						}
					}
				}
			}
		}
		translate(v = [0, 0, (PCB_Thickness - tiny_dimension)]) {
			rotate(a = [0, 0, 0]) {
				linear_extrude(height = (min(((topmost_z + c_Base_Thickness) - c_Base_Line_Height), 2.54) + (2 * tiny_dimension))) {
					union() {
						hull() {
							union() {
								peri_line_scad([1.2690000000000001, -5.636000242233276],[(1.2690000000000001 + (((0.01 + Effective_Shell_Thickness_For_FP4) + Effective_Shell_Gap_For_FP4) * 1.0)), (-5.636000242233276 + (((0.01 + Effective_Shell_Thickness_For_FP4) + Effective_Shell_Gap_For_FP4) * 0.0))],0.4);
								peri_line_scad([1.2690000000000001, -1.9839999848604197],[(1.2690000000000001 + (((0.01 + Effective_Shell_Thickness_For_FP4) + Effective_Shell_Gap_For_FP4) * 1.0)), (-1.9839999848604197 + (((0.01 + Effective_Shell_Thickness_For_FP4) + Effective_Shell_Gap_For_FP4) * 0.0))],0.4);
							}
						}
						hull() {
							union() {
								peri_line_scad([-1.2690000000000001, -1.9839999848604202],[(-1.2690000000000001 + (((0.01 + Effective_Shell_Thickness_For_FP4) + Effective_Shell_Gap_For_FP4) * -1.0)), (-1.9839999848604202 + (((0.01 + Effective_Shell_Thickness_For_FP4) + Effective_Shell_Gap_For_FP4) * 0.0))],0.4);
								peri_line_scad([-1.2690000000000001, -5.636000242233276],[(-1.2690000000000001 + (((0.01 + Effective_Shell_Thickness_For_FP4) + Effective_Shell_Gap_For_FP4) * -1.0)), (-5.636000242233276 + (((0.01 + Effective_Shell_Thickness_For_FP4) + Effective_Shell_Gap_For_FP4) * 0.0))],0.4);
							}
						}
					}
				}
			}
		}
	}
}
module hullpoly_FP4_0_0(){
	polygon(points = [[1.27, -8.636000242233276], [1.27, 1.0160000151395798], [1.0160000151395798, 1.27], [-1.0160000151395798, 1.27], [-1.27, 1.0160000151395798], [-1.27, -8.636000242233276], [-1.0160000151395798, -8.89], [1.0160000151395798, -8.89]]);
}
module hullpoly_FP4_0_1(){
	polygon(points = [[0.32004000514745706, -7.94003981590271], [0.32004000514745706, 0.32004000514745706], [-0.32004000514745706, 0.32004000514745706], [-0.32004000514745706, -7.94003981590271]]);
}
module fitting_pocket_FP4_0(){
	union() {
		translate(v = [0, 0, ((PCB_Thickness - tiny_dimension) + -2.9997399854660034)]) {
			rotate(a = [0, 0, 0]) {
				linear_extrude(height = (5.539739985466003 + (2 * tiny_dimension))) {
					offset(r = Effective_Shell_Gap_For_FP4) {
						union() {
							hullpoly_FP4_0_0();
						}
					}
				}
			}
		}
		translate(v = [0, 0, ((PCB_Thickness - tiny_dimension) + 2.54)]) {
			rotate(a = [0, 0, 0]) {
				linear_extrude(height = (5.999479970932007 + (2 * tiny_dimension))) {
					offset(r = Effective_Shell_Gap_For_FP4) {
						union() {
							hullpoly_FP4_0_1();
						}
					}
				}
			}
		}
	}
}
module ref_FP4_0(){
	union() {
		hullpoly_FP4_0_0();
	}
}
module wiggle_pocket_FP4_0(){
	translate(v = [0, 0, (PCB_Thickness + min_z_FP4)]) {
		rotate(a = [0, 0, 0]) {
			linear_extrude(height = (max_z_FP4 - min_z_FP4)) {
				offset(r = Effective_Shell_Gap_For_FP4) {
					union() {
						ref_FP4_0();
					}
				}
			}
		}
	}
}
module perimeter_FP4_0(){
	union() {
		translate(v = [0, 0, (PCB_Thickness + Effective_Shell_Clearance_From_PCB_For_FP4)]) {
			rotate(a = [0, 0, 0]) {
				linear_extrude(height = ((topmost_z - Effective_Shell_Clearance_From_PCB_For_FP4) + c_Base_Thickness)) {
					offset(r = (Effective_Shell_Gap_For_FP4 + Effective_Shell_Thickness_For_FP4)) {
						union() {
							ref_FP4_0();
						}
					}
				}
			}
		}
		translate(v = [0, 0, (((PCB_Thickness + topmost_z) + c_Base_Thickness) - Wrapper_Height_For_FP4)]) {
			rotate(a = [0, 0, 0]) {
				linear_extrude(height = Wrapper_Height_For_FP4) {
					difference() {
						offset(r = ((Effective_Shell_Gap_For_FP4 + Effective_Shell_Thickness_For_FP4) + Wrapper_Thickness_For_FP4)) {
							union() {
								ref_FP4_0();
							}
						}
						offset(r = (Effective_Shell_Gap_For_FP4 + Effective_Shell_Thickness_For_FP4)) {
							union() {
								ref_FP4_0();
							}
						}
					}
				}
			}
		}
	}
}
module fitting_flower_FP4_0(){
	union() {
		translate(v = [0, 0, ((PCB_Thickness + max(-2.9997399854660034, Effective_Shell_Clearance_From_PCB_For_FP4)) - tiny_dimension)]) {
			rotate(a = [0, 0, 0]) {
				linear_extrude(height = ((max_z_FP4 - max(-2.9997399854660034, Effective_Shell_Clearance_From_PCB_For_FP4)) + (2 * tiny_dimension))) {
					difference() {
						offset(r = (Effective_Shell_Gap_For_FP4 + Effective_Shell_Thickness_For_FP4)) {
							union() {
								hullpoly_FP4_0_0();
							}
						}
						offset(r = Effective_Shell_Gap_For_FP4) {
							union() {
								hullpoly_FP4_0_0();
							}
						}
					}
				}
			}
		}
		translate(v = [0, 0, ((PCB_Thickness + max(2.54, Effective_Shell_Clearance_From_PCB_For_FP4)) - tiny_dimension)]) {
			rotate(a = [0, 0, 0]) {
				linear_extrude(height = ((max_z_FP4 - max(2.54, Effective_Shell_Clearance_From_PCB_For_FP4)) + (2 * tiny_dimension))) {
					difference() {
						offset(r = (Effective_Shell_Gap_For_FP4 + Effective_Shell_Thickness_For_FP4)) {
							union() {
								hullpoly_FP4_0_1();
							}
						}
						offset(r = Effective_Shell_Gap_For_FP4) {
							union() {
								hullpoly_FP4_0_1();
							}
						}
					}
				}
			}
		}
		translate(v = [0, 0, (((PCB_Thickness + topmost_z) + c_Base_Thickness) - Wrapper_Height_For_FP4)]) {
			rotate(a = [0, 0, 0]) {
				linear_extrude(height = Wrapper_Height_For_FP4) {
					difference() {
						offset(r = ((Effective_Shell_Gap_For_FP4 + Effective_Shell_Thickness_For_FP4) + Wrapper_Thickness_For_FP4)) {
							union() {
								ref_FP4_0();
							}
						}
						offset(r = (Effective_Shell_Gap_For_FP4 + Effective_Shell_Thickness_For_FP4)) {
							union() {
								ref_FP4_0();
							}
						}
					}
				}
			}
		}
		translate(v = [0, 0, (PCB_Thickness + max_z_FP4)]) {
			rotate(a = [0, 0, 0]) {
				linear_extrude(height = ((topmost_z - max_z_FP4) + c_Base_Thickness)) {
					offset(r = (Effective_Shell_Gap_For_FP4 + Effective_Shell_Thickness_For_FP4)) {
						union() {
							ref_FP4_0();
						}
					}
				}
			}
		}
	}
}
module shape_FP4_0_0(){
	union() {
		polygon(points = [[1.016, -8.89], [1.266, -8.64], [1.27, -8.636], [1.27, -6.636], [1.27, -6.604], [1.02, -6.354], [1.016, -6.35], [1.266, -6.1], [1.27, -6.096], [1.27, -4.096], [1.27, -4.064], [1.02, -3.814], [1.016, -3.81], [1.266, -3.56], [1.27, -3.556], [1.27, -1.556], [1.27, -1.524], [1.02, -1.274], [1.016, -1.27], [1.266, -1.02], [1.27, -1.016], [1.27, 0.984], [1.27, 1.016], [1.02, 1.266], [1.016, 1.27], [-0.984, 1.27], [-1.016, 1.27], [-1.27, 1.016], [-1.27, -1.016], [-1.016, -1.27], [-1.27, -1.524], [-1.27, -3.556], [-1.016, -3.81], [-1.27, -4.064], [-1.27, -6.096], [-1.016, -6.35], [-1.27, -6.604], [-1.27, -8.636], [-1.016, -8.89]]);
	}
}
module keepout_volume_FP4_0_0(){
	translate(v = [0, 0, (PCB_Thickness + max(-2.9997399854660034, Effective_Shell_Clearance_From_PCB_For_FP4))]) {
		rotate(a = [0, 0, 0]) {
			linear_extrude(height = ((2.539479970932007 - max(-2.9997399854660034, Effective_Shell_Clearance_From_PCB_For_FP4)) + tiny_dimension)) {
				offset(r = Effective_Shell_Gap_For_FP4) {
					union() {
						shape_FP4_0_0();
					}
				}
			}
		}
	}
}
module shape_FP4_0_1(){
	union() {
		polygon(points = [[0.209, -0.658], [0.258, -0.65], [0.305, -0.638], [0.351, -0.622], [0.396, -0.601], [0.438, -0.576], [0.477, -0.547], [0.514, -0.514], [0.547, -0.477], [0.576, -0.438], [0.601, -0.396], [0.622, -0.351], [0.638, -0.305], [0.65, -0.258], [0.658, -0.209], [0.66, -0.16], [0.66, 0.16], [0.658, 0.209], [0.65, 0.258], [0.638, 0.305], [0.622, 0.351], [0.601, 0.396], [0.576, 0.438], [0.547, 0.477], [0.514, 0.514], [0.477, 0.547], [0.438, 0.576], [0.396, 0.601], [0.351, 0.622], [0.305, 0.638], [0.258, 0.65], [0.209, 0.658], [0.16, 0.66], [-0.16, 0.66], [-0.209, 0.658], [-0.258, 0.65], [-0.305, 0.638], [-0.351, 0.622], [-0.396, 0.601], [-0.438, 0.576], [-0.477, 0.547], [-0.514, 0.514], [-0.547, 0.477], [-0.576, 0.438], [-0.601, 0.396], [-0.622, 0.351], [-0.638, 0.305], [-0.65, 0.258], [-0.658, 0.209], [-0.66, 0.16], [-0.66, -0.16], [-0.658, -0.209], [-0.65, -0.258], [-0.638, -0.305], [-0.622, -0.351], [-0.601, -0.396], [-0.576, -0.438], [-0.547, -0.477], [-0.514, -0.514], [-0.477, -0.547], [-0.438, -0.576], [-0.396, -0.601], [-0.351, -0.622], [-0.305, -0.638], [-0.258, -0.65], [-0.209, -0.658], [-0.16, -0.66], [0.16, -0.66]]);
		polygon(points = [[0.209, -3.198], [0.258, -3.19], [0.305, -3.178], [0.351, -3.162], [0.396, -3.141], [0.438, -3.116], [0.477, -3.087], [0.514, -3.054], [0.547, -3.017], [0.576, -2.978], [0.601, -2.936], [0.622, -2.891], [0.638, -2.845], [0.65, -2.798], [0.658, -2.749], [0.66, -2.7], [0.66, -2.38], [0.658, -2.331], [0.65, -2.282], [0.638, -2.235], [0.622, -2.189], [0.601, -2.144], [0.576, -2.102], [0.547, -2.063], [0.514, -2.026], [0.477, -1.993], [0.438, -1.964], [0.396, -1.939], [0.351, -1.918], [0.305, -1.902], [0.258, -1.89], [0.209, -1.882], [0.16, -1.88], [-0.16, -1.88], [-0.209, -1.882], [-0.258, -1.89], [-0.305, -1.902], [-0.351, -1.918], [-0.396, -1.939], [-0.438, -1.964], [-0.477, -1.993], [-0.514, -2.026], [-0.547, -2.063], [-0.576, -2.102], [-0.601, -2.144], [-0.622, -2.189], [-0.638, -2.235], [-0.65, -2.282], [-0.658, -2.331], [-0.66, -2.38], [-0.66, -2.7], [-0.658, -2.749], [-0.65, -2.798], [-0.638, -2.845], [-0.622, -2.891], [-0.601, -2.936], [-0.576, -2.978], [-0.547, -3.017], [-0.514, -3.054], [-0.477, -3.087], [-0.438, -3.116], [-0.396, -3.141], [-0.351, -3.162], [-0.305, -3.178], [-0.258, -3.19], [-0.209, -3.198], [-0.16, -3.2], [0.16, -3.2]]);
		polygon(points = [[0.209, -5.738], [0.258, -5.73], [0.305, -5.718], [0.351, -5.702], [0.396, -5.681], [0.438, -5.656], [0.477, -5.627], [0.514, -5.594], [0.547, -5.557], [0.576, -5.518], [0.601, -5.476], [0.622, -5.431], [0.638, -5.385], [0.65, -5.338], [0.658, -5.289], [0.66, -5.24], [0.66, -4.92], [0.658, -4.871], [0.65, -4.822], [0.638, -4.775], [0.622, -4.729], [0.601, -4.684], [0.576, -4.642], [0.547, -4.603], [0.514, -4.566], [0.477, -4.533], [0.438, -4.504], [0.396, -4.479], [0.351, -4.458], [0.305, -4.442], [0.258, -4.43], [0.209, -4.422], [0.16, -4.42], [-0.16, -4.42], [-0.209, -4.422], [-0.258, -4.43], [-0.305, -4.442], [-0.351, -4.458], [-0.396, -4.479], [-0.438, -4.504], [-0.477, -4.533], [-0.514, -4.566], [-0.547, -4.603], [-0.576, -4.642], [-0.601, -4.684], [-0.622, -4.729], [-0.638, -4.775], [-0.65, -4.822], [-0.658, -4.871], [-0.66, -4.92], [-0.66, -5.24], [-0.658, -5.289], [-0.65, -5.338], [-0.638, -5.385], [-0.622, -5.431], [-0.601, -5.476], [-0.576, -5.518], [-0.547, -5.557], [-0.514, -5.594], [-0.477, -5.627], [-0.438, -5.656], [-0.396, -5.681], [-0.351, -5.702], [-0.305, -5.718], [-0.258, -5.73], [-0.209, -5.738], [-0.16, -5.74], [0.16, -5.74]]);
		polygon(points = [[0.209, -8.278], [0.258, -8.27], [0.305, -8.258], [0.351, -8.242], [0.396, -8.221], [0.438, -8.196], [0.477, -8.167], [0.514, -8.134], [0.547, -8.097], [0.576, -8.058], [0.601, -8.016], [0.622, -7.971], [0.638, -7.925], [0.65, -7.878], [0.658, -7.829], [0.66, -7.78], [0.66, -7.46], [0.658, -7.411], [0.65, -7.362], [0.638, -7.315], [0.622, -7.269], [0.601, -7.224], [0.576, -7.182], [0.547, -7.143], [0.514, -7.106], [0.477, -7.073], [0.438, -7.044], [0.396, -7.019], [0.351, -6.998], [0.305, -6.982], [0.258, -6.97], [0.209, -6.962], [0.16, -6.96], [-0.16, -6.96], [-0.209, -6.962], [-0.258, -6.97], [-0.305, -6.982], [-0.351, -6.998], [-0.396, -7.019], [-0.438, -7.044], [-0.477, -7.073], [-0.514, -7.106], [-0.547, -7.143], [-0.576, -7.182], [-0.601, -7.224], [-0.622, -7.269], [-0.638, -7.315], [-0.65, -7.362], [-0.658, -7.411], [-0.66, -7.46], [-0.66, -7.78], [-0.658, -7.829], [-0.65, -7.878], [-0.638, -7.925], [-0.622, -7.971], [-0.601, -8.016], [-0.576, -8.058], [-0.547, -8.097], [-0.514, -8.134], [-0.477, -8.167], [-0.438, -8.196], [-0.396, -8.221], [-0.351, -8.242], [-0.305, -8.258], [-0.258, -8.27], [-0.209, -8.278], [-0.16, -8.28], [0.16, -8.28]]);
	}
}
module keepout_volume_FP4_0_1(){
	translate(v = [0, 0, (PCB_Thickness + max(-2.9997399854660034, Effective_Shell_Clearance_From_PCB_For_FP4))]) {
		rotate(a = [0, 0, 0]) {
			linear_extrude(height = ((8.539479970932007 - max(-2.9997399854660034, Effective_Shell_Clearance_From_PCB_For_FP4)) + tiny_dimension)) {
				offset(r = Effective_Shell_Gap_For_FP4) {
					union() {
						shape_FP4_0_1();
					}
				}
			}
		}
	}
}
module tight_perimeter_FP4_0(){
	union() {
		translate(v = [0, 0, (PCB_Thickness + Effective_Shell_Clearance_From_PCB_For_FP4)]) {
			rotate(a = [0, 0, 0]) {
				linear_extrude(height = ((topmost_z - Effective_Shell_Clearance_From_PCB_For_FP4) + c_Base_Thickness)) {
					offset(r = (Effective_Shell_Gap_For_FP4 + Effective_Shell_Thickness_For_FP4)) {
						union() {
							shape_FP4_0_0();
						}
					}
				}
			}
		}
		translate(v = [0, 0, (((PCB_Thickness + topmost_z) + c_Base_Thickness) - Wrapper_Height_For_FP4)]) {
			rotate(a = [0, 0, 0]) {
				linear_extrude(height = Wrapper_Height_For_FP4) {
					difference() {
						offset(r = ((Effective_Shell_Gap_For_FP4 + Effective_Shell_Thickness_For_FP4) + Wrapper_Thickness_For_FP4)) {
							union() {
								shape_FP4_0_0();
							}
						}
						offset(r = (Effective_Shell_Gap_For_FP4 + Effective_Shell_Thickness_For_FP4)) {
							union() {
								shape_FP4_0_0();
							}
						}
					}
				}
			}
		}
	}
}
module tight_pocket_FP4_0(){
	union() {
		keepout_volume_FP4_0_0();
		keepout_volume_FP4_0_1();
	}
}
module courtyard_FP4(){
	polygon(points = [[1.8, 9.4], [1.8, -1.8], [-1.8, -1.8], [-1.8, 9.4]]);
}
module courtyard_pocket_FP4(){
	translate(v = [0, 0, PCB_Thickness]) {
		translate(v = [0, 0, min_z_FP4]) {
			linear_extrude(height = (max_z_FP4 - min_z_FP4)) {
				offset(r = Effective_Shell_Gap_For_FP4) {
					union() {
						courtyard_FP4();
					}
				}
			}
		}
	}
}
module courtyard_perimeter_FP4(){
	union() {
		translate(v = [0, 0, (PCB_Thickness + Effective_Shell_Clearance_From_PCB_For_FP4)]) {
			linear_extrude(height = ((topmost_z - Effective_Shell_Clearance_From_PCB_For_FP4) + c_Base_Thickness)) {
				offset(r = (Effective_Shell_Gap_For_FP4 + Effective_Shell_Thickness_For_FP4)) {
					union() {
						courtyard_FP4();
					}
				}
			}
		}
		translate(v = [0, 0, (((PCB_Thickness + topmost_z) + c_Base_Thickness) - Wrapper_Height_For_FP4)]) {
			linear_extrude(height = Wrapper_Height_For_FP4) {
				difference() {
					offset(r = ((Effective_Shell_Gap_For_FP4 + Effective_Shell_Thickness_For_FP4) + Wrapper_Thickness_For_FP4)) {
						union() {
							courtyard_FP4();
						}
					}
					offset(r = (Effective_Shell_Gap_For_FP4 + Effective_Shell_Thickness_For_FP4)) {
						union() {
							courtyard_FP4();
						}
					}
				}
			}
		}
	}
}
module fitting_cuts_FP5_0(){
	union() {
		translate(v = [0, 0, ((PCB_Thickness - tiny_dimension) + max(2.54, Effective_Shell_Clearance_From_PCB_For_FP5))]) {
			rotate(a = [0, 0, 0]) {
				linear_extrude(height = ((min(((topmost_z + c_Base_Thickness) - c_Base_Line_Height), 8.539479970932007) - max(2.54, Effective_Shell_Clearance_From_PCB_For_FP5)) + (2 * tiny_dimension))) {
					union() {
						peri_line_scad([-0.3193328983662705, 0.3193328983662705],[-0.46075425460358, 0.46075425460358],0.4);
						peri_line_scad([-0.3193328983662705, -10.479332709121524],[-0.46075425460358, -10.620754065358833],0.4);
						peri_line_scad([0.3193328983662705, -10.479332709121524],[0.46075425460358, -10.620754065358833],0.4);
						peri_line_scad([0.3193328983662705, 0.3193328983662705],[0.46075425460358, 0.46075425460358],0.4);
					}
				}
			}
		}
		translate(v = [0, 0, (PCB_Thickness - tiny_dimension)]) {
			rotate(a = [0, 0, 0]) {
				linear_extrude(height = (min(((topmost_z + c_Base_Thickness) - c_Base_Line_Height), 8.539479970932007) + (2 * tiny_dimension))) {
					union() {
						hull() {
							union() {
								peri_line_scad([-0.31904000514745706, -2.6799599948525428],[(-0.31904000514745706 + (((0.9600000000000006 + Effective_Shell_Thickness_For_FP5) + Effective_Shell_Gap_For_FP5) * -1.0)), (-2.6799599948525428 + (((0.9600000000000006 + Effective_Shell_Thickness_For_FP5) + Effective_Shell_Gap_For_FP5) * 0.0))],0.4);
								peri_line_scad([-0.31904000514745706, -7.48003981590271],[(-0.31904000514745706 + (((0.9600000000000006 + Effective_Shell_Thickness_For_FP5) + Effective_Shell_Gap_For_FP5) * -1.0)), (-7.48003981590271 + (((0.9600000000000006 + Effective_Shell_Thickness_For_FP5) + Effective_Shell_Gap_For_FP5) * 0.0))],0.4);
							}
						}
						hull() {
							union() {
								peri_line_scad([0.31904000514745706, -7.48003981590271],[(0.31904000514745706 + (((0.9600000000000006 + Effective_Shell_Thickness_For_FP5) + Effective_Shell_Gap_For_FP5) * 1.0)), (-7.48003981590271 + (((0.9600000000000006 + Effective_Shell_Thickness_For_FP5) + Effective_Shell_Gap_For_FP5) * 0.0))],0.4);
								peri_line_scad([0.31904000514745706, -2.6799599948525428],[(0.31904000514745706 + (((0.9600000000000006 + Effective_Shell_Thickness_For_FP5) + Effective_Shell_Gap_For_FP5) * 1.0)), (-2.6799599948525428 + (((0.9600000000000006 + Effective_Shell_Thickness_For_FP5) + Effective_Shell_Gap_For_FP5) * 0.0))],0.4);
							}
						}
					}
				}
			}
		}
		translate(v = [0, 0, ((PCB_Thickness - tiny_dimension) + max(-2.9997399854660034, Effective_Shell_Clearance_From_PCB_For_FP5))]) {
			rotate(a = [0, 0, 0]) {
				linear_extrude(height = ((min(((topmost_z + c_Base_Thickness) - c_Base_Line_Height), 2.54) - max(-2.9997399854660034, Effective_Shell_Clearance_From_PCB_For_FP5)) + (2 * tiny_dimension))) {
					union() {
						peri_line_scad([-1.2690761204674887, 1.0156173317072148],[-1.4538520269697461, 1.0921540181802327],0.4);
						hull() {
							union() {
								peri_line_scad([-1.2690761205530252, -11.175617558594409],[-1.4538520099479868, -11.25215428636808],0.4);
								peri_line_scad([-1.015617331913718, -11.429076120381952],[-1.0921539770860795, -11.613852043991496],0.4);
							}
						}
						peri_line_scad([-1.015617331913718, -11.429076120381952],[-1.0921539770860795, -11.613852043991496],0.4);
						hull() {
							union() {
								peri_line_scad([1.015617331913718, -11.429076120381952],[1.0921539770860795, -11.613852043991496],0.4);
								peri_line_scad([1.2690761205530252, -11.175617558594409],[1.4538520099479868, -11.25215428636808],0.4);
							}
						}
						peri_line_scad([1.2690761205530252, -11.175617558594409],[1.4538520099479868, -11.25215428636808],0.4);
						hull() {
							union() {
								peri_line_scad([1.2690761204674887, 1.0156173317072148],[1.4538520269697461, 1.0921540181802327],0.4);
								peri_line_scad([1.0156173317072148, 1.2690761204674887],[1.0921540181802327, 1.4538520269697461],0.4);
							}
						}
						peri_line_scad([1.0156173317072148, 1.2690761204674887],[1.0921540181802327, 1.4538520269697461],0.4);
						hull() {
							union() {
								peri_line_scad([-1.0156173317072148, 1.2690761204674887],[-1.0921540181802327, 1.4538520269697461],0.4);
								peri_line_scad([-1.2690761204674887, 1.0156173317072148],[-1.4538520269697461, 1.0921540181802327],0.4);
							}
						}
					}
				}
			}
		}
		translate(v = [0, 0, (PCB_Thickness - tiny_dimension)]) {
			rotate(a = [0, 0, 0]) {
				linear_extrude(height = (min(((topmost_z + c_Base_Thickness) - c_Base_Line_Height), 2.54) + (2 * tiny_dimension))) {
					union() {
						hull() {
							union() {
								peri_line_scad([-1.2690000000000001, -1.9839999848604202],[(-1.2690000000000001 + (((0.01 + Effective_Shell_Thickness_For_FP5) + Effective_Shell_Gap_For_FP5) * -1.0)), (-1.9839999848604202 + (((0.01 + Effective_Shell_Thickness_For_FP5) + Effective_Shell_Gap_For_FP5) * 0.0))],0.4);
								peri_line_scad([-1.2690000000000001, -8.176000242233277],[(-1.2690000000000001 + (((0.01 + Effective_Shell_Thickness_For_FP5) + Effective_Shell_Gap_For_FP5) * -1.0)), (-8.176000242233277 + (((0.01 + Effective_Shell_Thickness_For_FP5) + Effective_Shell_Gap_For_FP5) * 0.0))],0.4);
							}
						}
						hull() {
							union() {
								peri_line_scad([1.2690000000000001, -8.176000242233277],[(1.2690000000000001 + (((0.01 + Effective_Shell_Thickness_For_FP5) + Effective_Shell_Gap_For_FP5) * 1.0)), (-8.176000242233277 + (((0.01 + Effective_Shell_Thickness_For_FP5) + Effective_Shell_Gap_For_FP5) * 0.0))],0.4);
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
