shreekumar3d/jigita/test-boards/pacman/gen/pacman.scad

// Customizable Jig Generator
// In OpenSCAD, use "Description Only" for best user experience
// understanding the tunable parameters.
// -----------------------------------------------------
// Auto generated file by jigit, the awesome automatic
// jig generator for your PCB designs. Checkout the project
// at https://github.com/shreekumar3d/jigit
// -----------------------------------------------------
// Input board file   : pacman.kicad_pcb
// Configuration file : (Tool Default Internal Configuration)
//
// Complete configuration file is embedded at the end of this
// file.

// { These are configurable parameters
// you can tweak these here and count on
// openscad magic to do show you the result
// right away!

/* [Preview Options - No effect on STL output] */
// Show PCB for reference (green)
Show_PCB = true; // [true,false]
// Transparency of PCB
PCB_Transparency = 0.5; //[0.0:1.0]

// Show component volumes (orange)
Show_Component_Volumes = true; // [true,false]
// Transparency of component volumes
Component_Volume_Transparency = 0.2; // [0.0:1.0]

// Show volume reserved to avoid touching SMD parts (red)
Show_SMD_Keepout_Volumes = true; // [true,false]
// Transparency of SMD keepout volumes
SMD_Keepout_Volume_Transparency = 0.4; // [0.0:1.0]

/* [PCB] */
PCB_Thickness=1.6;

/* [Jig] */
Type_of_Jig = "TH_soldering"; // [TH_soldering,component_fitting]

/* [Through Hole Soldering Jig] */

// Gap between PCB edge and slot on the jig
PCB_Gap=0.3;

// Width of the groove on the jig, holding the PCB
PCB_Overlap=0.3;

// Wall thickness of the jig, abutting the PCB
PCB_Holder_Perimeter=1.6;

// Height of solid perimeter at the base
Lower_Perimeter_Height = 2;

Groove="At PCB Corners: 15 mm"; //["At PCB Corners: 15 mm", "All Around PCB Edge"]

Mounting_Hole_Jig=false; //[false, true]
MH_Spacer_End=4.916119992733002;
MH_Spacer_Start=-0.2;
Spacer_Is_Fused = true;
Bolt_Is_External = true;

/* [Base] */

// Type of Base
Base_Type = "griddish"; // [x_lines, y_lines, griddish, minmesh, mesh, solid]

// Thickness of Base
Base_Thickness = 0.4;

// Width of Lines on Base
Base_Line_Width = 2.0;

// Height of Lines on Base
Base_Line_Height = 1.0;

/* [SMD Keepout] */

// SMD keepout volume extension in Z
SMD_Clearance_From_Shells=1;

// SMD keepout volume extension in XY
SMD_Gap_From_Shells=0.5;
/* [Include these components in output STL file] */
//Capacitor_THT:CP_Axial_L10.0mm_D4.5mm_P15.00mm_Horizontal (C1)
Include_C1_in_Jig=true; // [false,true]
//Connector_PinHeader_2.54mm:PinHeader_1x02_P2.54mm_Vertical (J1)
Include_J1_in_Jig=true; // [false,true]
//Connector_PinHeader_2.54mm:PinHeader_1x02_P2.54mm_Vertical (J3)
Include_J3_in_Jig=true; // [false,true]
//Connector_PinHeader_2.54mm:PinHeader_1x02_P2.54mm_Vertical (J4)
Include_J4_in_Jig=true; // [false,true]
//Connector_PinHeader_2.54mm:PinHeader_1x02_P2.54mm_Vertical (J2)
Include_J2_in_Jig=true; // [false,true]
/* [Footprint: Connector_PinHeader_2.54mm:PinHeader_1x02_P2.54mm_Vertical] */
//XY Gap in shell for component insertion
Shell_Gap_For_FP1 = 0.1;
//Thickness of shell
Shell_Thickness_For_FP1 = 1.2;
//Z distance from start of shell to PCB
Shell_Clearance_From_PCB_For_FP1 = 1;
/* [Footprint: Capacitor_THT:CP_Axial_L10.0mm_D4.5mm_P15.00mm_Horizontal] */
//XY Gap in shell for component insertion
Shell_Gap_For_FP2 = 0.1;
//Thickness of shell
Shell_Thickness_For_FP2 = 1.2;
//Z distance from start of shell to PCB
Shell_Clearance_From_PCB_For_FP2 = 1;
/* [C1 (Capacitor_THT:CP_Axial_L10.0mm_D4.5mm_P15.00mm_Horizontal)] */
//Type of shell for this component
Shell_Type_For_C1="fitting"; // [wiggle,fitting,fitting_flower,tight,courtyard]
//Insert this component into jig from this side.(Bottom insertion requires wiggle or courtyard shell to work)
Insert_C1_From="top"; // [top,bottom]
//Delta(+/-) thickness for shell, additional to footprint setting
Delta_Shell_Thickness_For_C1=0;
//Delta XY gap to allow insertion of this component into its shell
Delta_Shell_Gap_For_C1=0;
//Delta Z clearance from the shell to PCB
Delta_Shell_Clearance_From_PCB_For_C1=0;
//Wrapper thickness
Wrapper_Thickness_For_C1=0.0; // [0:0.1:10.0]
//Wrapper height
Wrapper_Height_For_C1=0.0; // [0:0.1:8.539479970932007]
/* [J1 (Connector_PinHeader_2.54mm:PinHeader_1x02_P2.54mm_Vertical)] */
//Type of shell for this component
Shell_Type_For_J1="fitting"; // [wiggle,fitting,fitting_flower,tight,courtyard]
//Insert this component into jig from this side.(Bottom insertion requires wiggle or courtyard shell to work)
Insert_J1_From="top"; // [top,bottom]
//Delta(+/-) thickness for shell, additional to footprint setting
Delta_Shell_Thickness_For_J1=0;
//Delta XY gap to allow insertion of this component into its shell
Delta_Shell_Gap_For_J1=0;
//Delta Z clearance from the shell to PCB
Delta_Shell_Clearance_From_PCB_For_J1=0;
//Wrapper thickness
Wrapper_Thickness_For_J1=0.0; // [0:0.1:10.0]
//Wrapper height
Wrapper_Height_For_J1=0.0; // [0:0.1:8.539479970932007]
/* [J3 (Connector_PinHeader_2.54mm:PinHeader_1x02_P2.54mm_Vertical)] */
//Type of shell for this component
Shell_Type_For_J3="fitting"; // [wiggle,fitting,fitting_flower,tight,courtyard]
//Insert this component into jig from this side.(Bottom insertion requires wiggle or courtyard shell to work)
Insert_J3_From="top"; // [top,bottom]
//Delta(+/-) thickness for shell, additional to footprint setting
Delta_Shell_Thickness_For_J3=0;
//Delta XY gap to allow insertion of this component into its shell
Delta_Shell_Gap_For_J3=0;
//Delta Z clearance from the shell to PCB
Delta_Shell_Clearance_From_PCB_For_J3=0;
//Wrapper thickness
Wrapper_Thickness_For_J3=0.0; // [0:0.1:10.0]
//Wrapper height
Wrapper_Height_For_J3=0.0; // [0:0.1:8.539479970932007]
/* [J4 (Connector_PinHeader_2.54mm:PinHeader_1x02_P2.54mm_Vertical)] */
//Type of shell for this component
Shell_Type_For_J4="fitting"; // [wiggle,fitting,fitting_flower,tight,courtyard]
//Insert this component into jig from this side.(Bottom insertion requires wiggle or courtyard shell to work)
Insert_J4_From="top"; // [top,bottom]
//Delta(+/-) thickness for shell, additional to footprint setting
Delta_Shell_Thickness_For_J4=0;
//Delta XY gap to allow insertion of this component into its shell
Delta_Shell_Gap_For_J4=0;
//Delta Z clearance from the shell to PCB
Delta_Shell_Clearance_From_PCB_For_J4=0;
//Wrapper thickness
Wrapper_Thickness_For_J4=0.0; // [0:0.1:10.0]
//Wrapper height
Wrapper_Height_For_J4=0.0; // [0:0.1:8.539479970932007]
/* [J2 (Connector_PinHeader_2.54mm:PinHeader_1x02_P2.54mm_Vertical)] */
//Type of shell for this component
Shell_Type_For_J2="fitting"; // [wiggle,fitting,fitting_flower,tight,courtyard]
//Insert this component into jig from this side.(Bottom insertion requires wiggle or courtyard shell to work)
Insert_J2_From="top"; // [top,bottom]
//Delta(+/-) thickness for shell, additional to footprint setting
Delta_Shell_Thickness_For_J2=0;
//Delta XY gap to allow insertion of this component into its shell
Delta_Shell_Gap_For_J2=0;
//Delta Z clearance from the shell to PCB
Delta_Shell_Clearance_From_PCB_For_J2=0;
//Wrapper thickness
Wrapper_Thickness_For_J2=0.0; // [0:0.1:10.0]
//Wrapper height
Wrapper_Height_For_J2=0.0; // [0:0.1:8.539479970932007]
// } End of configurable parameters
/* [Hidden] */
$fs = 0.05;
first_layer_height = 0.2;
layer_height = 0.2;
Effective_Shell_Thickness_For_C1 = Shell_Thickness_For_FP2 + Delta_Shell_Thickness_For_C1;
Effective_Shell_Gap_For_C1 = Shell_Gap_For_FP2 + Delta_Shell_Gap_For_C1;
Effective_Shell_Clearance_From_PCB_For_C1 = Shell_Clearance_From_PCB_For_FP2 + Delta_Shell_Clearance_From_PCB_For_C1;
Effective_Shell_Thickness_For_J1 = Shell_Thickness_For_FP1 + Delta_Shell_Thickness_For_J1;
Effective_Shell_Gap_For_J1 = Shell_Gap_For_FP1 + Delta_Shell_Gap_For_J1;
Effective_Shell_Clearance_From_PCB_For_J1 = Shell_Clearance_From_PCB_For_FP1 + Delta_Shell_Clearance_From_PCB_For_J1;
Effective_Shell_Thickness_For_J3 = Shell_Thickness_For_FP1 + Delta_Shell_Thickness_For_J3;
Effective_Shell_Gap_For_J3 = Shell_Gap_For_FP1 + Delta_Shell_Gap_For_J3;
Effective_Shell_Clearance_From_PCB_For_J3 = Shell_Clearance_From_PCB_For_FP1 + Delta_Shell_Clearance_From_PCB_For_J3;
Effective_Shell_Thickness_For_J4 = Shell_Thickness_For_FP1 + Delta_Shell_Thickness_For_J4;
Effective_Shell_Gap_For_J4 = Shell_Gap_For_FP1 + Delta_Shell_Gap_For_J4;
Effective_Shell_Clearance_From_PCB_For_J4 = Shell_Clearance_From_PCB_For_FP1 + Delta_Shell_Clearance_From_PCB_For_J4;
Effective_Shell_Thickness_For_J2 = Shell_Thickness_For_FP1 + Delta_Shell_Thickness_For_J2;
Effective_Shell_Gap_For_J2 = Shell_Gap_For_FP1 + Delta_Shell_Gap_For_J2;
Effective_Shell_Clearance_From_PCB_For_J2 = Shell_Clearance_From_PCB_For_FP1 + Delta_Shell_Clearance_From_PCB_For_J2;

// Height of the tallest component on the top side
topmost_z=8.539479970932007;
    
groove_width = max(PCB_Gap+PCB_Holder_Perimeter, PCB_Overlap)*2.2;
tiny_dimension = 0.0001;
base_z =  PCB_Thickness+topmost_z+Base_Thickness+2*tiny_dimension;

c_Spacer_Is_Fused = Bolt_Is_External ? Spacer_Is_Fused : true; // can't have separate bolt with internal bolt
c_Base_Thickness = Mounting_Hole_Jig ? first_layer_height: Base_Thickness;
c_MH_Jig_Second_Level_Height = first_layer_height+2*layer_height;
c_Base_Line_Height = Mounting_Hole_Jig ? topmost_z-MH_Spacer_End+c_MH_Jig_Second_Level_Height+c_Base_Thickness: Base_Line_Height;
c_Lower_Perimeter_Height = Mounting_Hole_Jig ? c_Base_Line_Height:Lower_Perimeter_Height;
mesh_start_z = PCB_Thickness+topmost_z+c_Base_Thickness-c_Base_Line_Height;
bottom_insertion_z = 9.339479970932008;
// Height of the individual components
max_z_J1= (Insert_J1_From=="bottom")? bottom_insertion_z : 8.539479970932007; //Applies to 3D Model(s): ${KICAD8_3DMODEL_DIR}/Connector_PinHeader_2.54mm.3dshapes/PinHeader_1x02_P2.54mm_Vertical.wrl
min_z_J1= -2.9997399854660034;
max_z_C1= (Insert_C1_From=="bottom")? bottom_insertion_z : 4.516119992733001; //Applies to 3D Model(s): ${KICAD8_3DMODEL_DIR}/Capacitor_THT.3dshapes/CP_Axial_L10.0mm_D4.5mm_P15.00mm_Horizontal.wrl
min_z_C1= -1.9989800012111665;
max_z_J3= (Insert_J3_From=="bottom")? bottom_insertion_z : 8.539479970932007; //Applies to 3D Model(s): ${KICAD8_3DMODEL_DIR}/Connector_PinHeader_2.54mm.3dshapes/PinHeader_1x02_P2.54mm_Vertical.wrl
min_z_J3= -2.9997399854660034;
max_z_J4= (Insert_J4_From=="bottom")? bottom_insertion_z : 8.539479970932007; //Applies to 3D Model(s): ${KICAD8_3DMODEL_DIR}/Connector_PinHeader_2.54mm.3dshapes/PinHeader_1x02_P2.54mm_Vertical.wrl
min_z_J4= -2.9997399854660034;
max_z_J2= (Insert_J2_From=="bottom")? bottom_insertion_z : 8.539479970932007; //Applies to 3D Model(s): ${KICAD8_3DMODEL_DIR}/Connector_PinHeader_2.54mm.3dshapes/PinHeader_1x02_P2.54mm_Vertical.wrl
min_z_J2= -2.9997399854660034;
// } END : Computed Values

module peri_line_scad(start,end,line_width){
	hull() {
		translate(v = start) {
			circle(d = line_width);
		}
		translate(v = end) {
			circle(d = line_width);
		}
	}
}
module fitting_cuts_J1_0(){
	union() {
		translate(v = [65.0, -62.0, ((PCB_Thickness - tiny_dimension) + max(2.54, Effective_Shell_Clearance_From_PCB_For_J1))]) {
			rotate(a = [0, 0, 0.0]) {
				linear_extrude(height = ((min(((topmost_z + c_Base_Thickness) - c_Base_Line_Height), 8.539479970932007) - max(2.54, Effective_Shell_Clearance_From_PCB_For_J1)) + (2 * tiny_dimension))) {
					union() {
						peri_line_scad([0.3193328983662705, -2.8593330119131193],[0.46075425460358, -3.000754368150429],0.4);
						peri_line_scad([0.3193328983662705, 0.3193328983662705],[0.46075425460358, 0.46075425460358],0.4);
						peri_line_scad([-0.3193328983662705, 0.3193328983662705],[-0.46075425460358, 0.46075425460358],0.4);
						peri_line_scad([-0.3193328983662705, -2.8593330119131193],[-0.46075425460358, -3.000754368150429],0.4);
					}
				}
			}
		}
		translate(v = [65.0, -62.0, (PCB_Thickness - tiny_dimension)]) {
			rotate(a = [0, 0, 0.0]) {
				linear_extrude(height = (min(((topmost_z + c_Base_Thickness) - c_Base_Line_Height), 8.539479970932007) + (2 * tiny_dimension))) {
					union();
				}
			}
		}
		translate(v = [65.0, -62.0, ((PCB_Thickness - tiny_dimension) + max(-2.9997399854660034, Effective_Shell_Clearance_From_PCB_For_J1))]) {
			rotate(a = [0, 0, 0.0]) {
				linear_extrude(height = ((min(((topmost_z + c_Base_Thickness) - c_Base_Line_Height), 2.54) - max(-2.9997399854660034, Effective_Shell_Clearance_From_PCB_For_J1)) + (2 * tiny_dimension))) {
					union() {
						peri_line_scad([1.2690761204389767, -3.55561725607815],[1.4538520326436606, -3.632153928784291],0.4);
						hull() {
							union() {
								peri_line_scad([1.2690761204674887, 1.0156173317072148],[1.4538520269697461, 1.0921540181802327],0.4);
								peri_line_scad([1.0156173317072148, 1.2690761204674887],[1.0921540181802327, 1.4538520269697461],0.4);
							}
						}
						peri_line_scad([1.0156173317072148, 1.2690761204674887],[1.0921540181802327, 1.4538520269697461],0.4);
						hull() {
							union() {
								peri_line_scad([-1.0156173317072148, 1.2690761204674887],[-1.0921540181802327, 1.4538520269697461],0.4);
								peri_line_scad([-1.2690761204674887, 1.0156173317072148],[-1.4538520269697461, 1.0921540181802327],0.4);
							}
						}
						peri_line_scad([-1.2690761204674887, 1.0156173317072148],[-1.4538520269697461, 1.0921540181802327],0.4);
						hull() {
							union() {
								peri_line_scad([-1.2690761204389767, -3.55561725607815],[-1.4538520326436606, -3.632153928784291],0.4);
								peri_line_scad([-1.0156173316383803, -3.809076120496001],[-1.0921540318782748, -3.993852021295831],0.4);
							}
						}
						peri_line_scad([-1.0156173316383803, -3.809076120496001],[-1.0921540318782748, -3.993852021295831],0.4);
						hull() {
							union() {
								peri_line_scad([1.0156173316383803, -3.809076120496001],[1.0921540318782748, -3.993852021295831],0.4);
								peri_line_scad([1.2690761204389767, -3.55561725607815],[1.4538520326436606, -3.632153928784291],0.4);
							}
						}
					}
				}
			}
		}
		translate(v = [65.0, -62.0, (PCB_Thickness - tiny_dimension)]) {
			rotate(a = [0, 0, 0.0]) {
				linear_extrude(height = (min(((topmost_z + c_Base_Thickness) - c_Base_Line_Height), 2.54) + (2 * tiny_dimension))) {
					union();
				}
			}
		}
	}
}
module hullpoly_J1_0_0(){
	polygon(points = [[1.27, -3.555999939441681], [1.27, 1.0160000151395798], [1.0160000151395798, 1.27], [-1.0160000151395798, 1.27], [-1.27, 1.0160000151395798], [-1.27, -3.555999939441681], [-1.0160000151395798, -3.81], [1.0160000151395798, -3.81]]);
}
module hullpoly_J1_0_1(){
	polygon(points = [[0.32004000514745706, -2.8600401186943056], [0.32004000514745706, 0.32004000514745706], [-0.32004000514745706, 0.32004000514745706], [-0.32004000514745706, -2.8600401186943056]]);
}
module fitting_pocket_J1_0(){
	union() {
		translate(v = [65.0, -62.0, ((PCB_Thickness - tiny_dimension) + -2.9997399854660034)]) {
			rotate(a = [0, 0, 0.0]) {
				linear_extrude(height = (5.539739985466003 + (2 * tiny_dimension))) {
					offset(r = Effective_Shell_Gap_For_J1) {
						union() {
							hullpoly_J1_0_0();
						}
					}
				}
			}
		}
		translate(v = [65.0, -62.0, ((PCB_Thickness - tiny_dimension) + 2.54)]) {
			rotate(a = [0, 0, 0.0]) {
				linear_extrude(height = (5.999479970932007 + (2 * tiny_dimension))) {
					offset(r = Effective_Shell_Gap_For_J1) {
						union() {
							hullpoly_J1_0_1();
						}
					}
				}
			}
		}
	}
}
module ref_J1_0(){
	union() {
		hullpoly_J1_0_0();
	}
}
module wiggle_pocket_J1_0(){
	translate(v = [65.0, -62.0, (PCB_Thickness + min_z_J1)]) {
		rotate(a = [0, 0, 0.0]) {
			linear_extrude(height = (max_z_J1 - min_z_J1)) {
				offset(r = Effective_Shell_Gap_For_J1) {
					union() {
						ref_J1_0();
					}
				}
			}
		}
	}
}
module perimeter_J1_0(){
	union() {
		translate(v = [65.0, -62.0, (PCB_Thickness + Effective_Shell_Clearance_From_PCB_For_J1)]) {
			rotate(a = [0, 0, 0.0]) {
				linear_extrude(height = ((topmost_z - Effective_Shell_Clearance_From_PCB_For_J1) + c_Base_Thickness)) {
					offset(r = (Effective_Shell_Gap_For_J1 + Effective_Shell_Thickness_For_J1)) {
						union() {
							ref_J1_0();
						}
					}
				}
			}
		}
		translate(v = [65.0, -62.0, (((PCB_Thickness + topmost_z) + c_Base_Thickness) - Wrapper_Height_For_J1)]) {
			rotate(a = [0, 0, 0.0]) {
				linear_extrude(height = Wrapper_Height_For_J1) {
					difference() {
						offset(r = ((Effective_Shell_Gap_For_J1 + Effective_Shell_Thickness_For_J1) + Wrapper_Thickness_For_J1)) {
							union() {
								ref_J1_0();
							}
						}
						offset(r = (Effective_Shell_Gap_For_J1 + Effective_Shell_Thickness_For_J1)) {
							union() {
								ref_J1_0();
							}
						}
					}
				}
			}
		}
	}
}
module fitting_flower_J1_0(){
	union() {
		translate(v = [65.0, -62.0, ((PCB_Thickness + max(-2.9997399854660034, Effective_Shell_Clearance_From_PCB_For_J1)) - tiny_dimension)]) {
			rotate(a = [0, 0, 0.0]) {
				linear_extrude(height = ((max_z_J1 - max(-2.9997399854660034, Effective_Shell_Clearance_From_PCB_For_J1)) + (2 * tiny_dimension))) {
					difference() {
						offset(r = (Effective_Shell_Gap_For_J1 + Effective_Shell_Thickness_For_J1)) {
							union() {
								hullpoly_J1_0_0();
							}
						}
						offset(r = Effective_Shell_Gap_For_J1) {
							union() {
								hullpoly_J1_0_0();
							}
						}
					}
				}
			}
		}
		translate(v = [65.0, -62.0, ((PCB_Thickness + max(2.54, Effective_Shell_Clearance_From_PCB_For_J1)) - tiny_dimension)]) {
			rotate(a = [0, 0, 0.0]) {
				linear_extrude(height = ((max_z_J1 - max(2.54, Effective_Shell_Clearance_From_PCB_For_J1)) + (2 * tiny_dimension))) {
					difference() {
						offset(r = (Effective_Shell_Gap_For_J1 + Effective_Shell_Thickness_For_J1)) {
							union() {
								hullpoly_J1_0_1();
							}
						}
						offset(r = Effective_Shell_Gap_For_J1) {
							union() {
								hullpoly_J1_0_1();
							}
						}
					}
				}
			}
		}
		translate(v = [65.0, -62.0, (((PCB_Thickness + topmost_z) + c_Base_Thickness) - Wrapper_Height_For_J1)]) {
			rotate(a = [0, 0, 0.0]) {
				linear_extrude(height = Wrapper_Height_For_J1) {
					difference() {
						offset(r = ((Effective_Shell_Gap_For_J1 + Effective_Shell_Thickness_For_J1) + Wrapper_Thickness_For_J1)) {
							union() {
								ref_J1_0();
							}
						}
						offset(r = (Effective_Shell_Gap_For_J1 + Effective_Shell_Thickness_For_J1)) {
							union() {
								ref_J1_0();
							}
						}
					}
				}
			}
		}
		translate(v = [65.0, -62.0, (PCB_Thickness + max_z_J1)]) {
			rotate(a = [0, 0, 0.0]) {
				linear_extrude(height = ((topmost_z - max_z_J1) + c_Base_Thickness)) {
					offset(r = (Effective_Shell_Gap_For_J1 + Effective_Shell_Thickness_For_J1)) {
						union() {
							ref_J1_0();
						}
					}
				}
			}
		}
	}
}
module shape_J1_0_0(){
	union() {
		polygon(points = [[1.016, -3.81], [1.266, -3.56], [1.27, -3.556], [1.27, -1.556], [1.27, -1.524], [1.02, -1.274], [1.016, -1.27], [1.266, -1.02], [1.27, -1.016], [1.27, 0.984], [1.27, 1.016], [1.02, 1.266], [1.016, 1.27], [-0.984, 1.27], [-1.016, 1.27], [-1.27, 1.016], [-1.27, -1.016], [-1.016, -1.27], [-1.27, -1.524], [-1.27, -3.556], [-1.016, -3.81]]);
	}
}
module keepout_volume_J1_0_0(){
	translate(v = [65.0, -62.0, (PCB_Thickness + max(-2.9997399854660034, Effective_Shell_Clearance_From_PCB_For_J1))]) {
		rotate(a = [0, 0, 0.0]) {
			linear_extrude(height = ((2.539479970932007 - max(-2.9997399854660034, Effective_Shell_Clearance_From_PCB_For_J1)) + tiny_dimension)) {
				offset(r = Effective_Shell_Gap_For_J1) {
					union() {
						shape_J1_0_0();
					}
				}
			}
		}
	}
}
module shape_J1_0_1(){
	union() {
		polygon(points = [[0.209, -0.658], [0.258, -0.65], [0.305, -0.638], [0.351, -0.622], [0.396, -0.601], [0.438, -0.576], [0.477, -0.547], [0.514, -0.514], [0.547, -0.477], [0.576, -0.438], [0.601, -0.396], [0.622, -0.351], [0.638, -0.305], [0.65, -0.258], [0.658, -0.209], [0.66, -0.16], [0.66, 0.16], [0.658, 0.209], [0.65, 0.258], [0.638, 0.305], [0.622, 0.351], [0.601, 0.396], [0.576, 0.438], [0.547, 0.477], [0.514, 0.514], [0.477, 0.547], [0.438, 0.576], [0.396, 0.601], [0.351, 0.622], [0.305, 0.638], [0.258, 0.65], [0.209, 0.658], [0.16, 0.66], [-0.16, 0.66], [-0.209, 0.658], [-0.258, 0.65], [-0.305, 0.638], [-0.351, 0.622], [-0.396, 0.601], [-0.438, 0.576], [-0.477, 0.547], [-0.514, 0.514], [-0.547, 0.477], [-0.576, 0.438], [-0.601, 0.396], [-0.622, 0.351], [-0.638, 0.305], [-0.65, 0.258], [-0.658, 0.209], [-0.66, 0.16], [-0.66, -0.16], [-0.658, -0.209], [-0.65, -0.258], [-0.638, -0.305], [-0.622, -0.351], [-0.601, -0.396], [-0.576, -0.438], [-0.547, -0.477], [-0.514, -0.514], [-0.477, -0.547], [-0.438, -0.576], [-0.396, -0.601], [-0.351, -0.622], [-0.305, -0.638], [-0.258, -0.65], [-0.209, -0.658], [-0.16, -0.66], [0.16, -0.66]]);
		polygon(points = [[0.209, -3.198], [0.258, -3.19], [0.305, -3.178], [0.351, -3.162], [0.396, -3.141], [0.438, -3.116], [0.477, -3.087], [0.514, -3.054], [0.547, -3.017], [0.576, -2.978], [0.601, -2.936], [0.622, -2.891], [0.638, -2.845], [0.65, -2.798], [0.658, -2.749], [0.66, -2.7], [0.66, -2.38], [0.658, -2.331], [0.65, -2.282], [0.638, -2.235], [0.622, -2.189], [0.601, -2.144], [0.576, -2.102], [0.547, -2.063], [0.514, -2.026], [0.477, -1.993], [0.438, -1.964], [0.396, -1.939], [0.351, -1.918], [0.305, -1.902], [0.258, -1.89], [0.209, -1.882], [0.16, -1.88], [-0.16, -1.88], [-0.209, -1.882], [-0.258, -1.89], [-0.305, -1.902], [-0.351, -1.918], [-0.396, -1.939], [-0.438, -1.964], [-0.477, -1.993], [-0.514, -2.026], [-0.547, -2.063], [-0.576, -2.102], [-0.601, -2.144], [-0.622, -2.189], [-0.638, -2.235], [-0.65, -2.282], [-0.658, -2.331], [-0.66, -2.38], [-0.66, -2.7], [-0.658, -2.749], [-0.65, -2.798], [-0.638, -2.845], [-0.622, -2.891], [-0.601, -2.936], [-0.576, -2.978], [-0.547, -3.017], [-0.514, -3.054], [-0.477, -3.087], [-0.438, -3.116], [-0.396, -3.141], [-0.351, -3.162], [-0.305, -3.178], [-0.258, -3.19], [-0.209, -3.198], [-0.16, -3.2], [0.16, -3.2]]);
	}
}
module keepout_volume_J1_0_1(){
	translate(v = [65.0, -62.0, (PCB_Thickness + max(-2.9997399854660034, Effective_Shell_Clearance_From_PCB_For_J1))]) {
		rotate(a = [0, 0, 0.0]) {
			linear_extrude(height = ((8.539479970932007 - max(-2.9997399854660034, Effective_Shell_Clearance_From_PCB_For_J1)) + tiny_dimension)) {
				offset(r = Effective_Shell_Gap_For_J1) {
					union() {
						shape_J1_0_1();
					}
				}
			}
		}
	}
}
module tight_perimeter_J1_0(){
	union() {
		translate(v = [65.0, -62.0, (PCB_Thickness + Effective_Shell_Clearance_From_PCB_For_J1)]) {
			rotate(a = [0, 0, 0.0]) {
				linear_extrude(height = ((topmost_z - Effective_Shell_Clearance_From_PCB_For_J1) + c_Base_Thickness)) {
					offset(r = (Effective_Shell_Gap_For_J1 + Effective_Shell_Thickness_For_J1)) {
						union() {
							shape_J1_0_0();
						}
					}
				}
			}
		}
		translate(v = [65.0, -62.0, (((PCB_Thickness + topmost_z) + c_Base_Thickness) - Wrapper_Height_For_J1)]) {
			rotate(a = [0, 0, 0.0]) {
				linear_extrude(height = Wrapper_Height_For_J1) {
					difference() {
						offset(r = ((Effective_Shell_Gap_For_J1 + Effective_Shell_Thickness_For_J1) + Wrapper_Thickness_For_J1)) {
							union() {
								shape_J1_0_0();
							}
						}
						offset(r = (Effective_Shell_Gap_For_J1 + Effective_Shell_Thickness_For_J1)) {
							union() {
								shape_J1_0_0();
							}
						}
					}
				}
			}
		}
	}
}
module tight_pocket_J1_0(){
	union() {
		keepout_volume_J1_0_0();
		keepout_volume_J1_0_1();
	}
}
module courtyard_J1(){
	polygon(points = [[66.795, -60.205], [66.795, -66.345], [63.205, -66.345], [63.205, -60.205]]);
}
module courtyard_pocket_J1(){
	translate(v = [0, 0, PCB_Thickness]) {
		translate(v = [0, 0, min_z_J1]) {
			linear_extrude(height = (max_z_J1 - min_z_J1)) {
				offset(r = Effective_Shell_Gap_For_J1) {
					union() {
						courtyard_J1();
					}
				}
			}
		}
	}
}
module courtyard_perimeter_J1(){
	union() {
		translate(v = [0, 0, (PCB_Thickness + Effective_Shell_Clearance_From_PCB_For_J1)]) {
			linear_extrude(height = ((topmost_z - Effective_Shell_Clearance_From_PCB_For_J1) + c_Base_Thickness)) {
				offset(r = (Effective_Shell_Gap_For_J1 + Effective_Shell_Thickness_For_J1)) {
					union() {
						courtyard_J1();
					}
				}
			}
		}
		translate(v = [0, 0, (((PCB_Thickness + topmost_z) + c_Base_Thickness) - Wrapper_Height_For_J1)]) {
			linear_extrude(height = Wrapper_Height_For_J1) {
				difference() {
					offset(r = ((Effective_Shell_Gap_For_J1 + Effective_Shell_Thickness_For_J1) + Wrapper_Thickness_For_J1)) {
						union() {
							courtyard_J1();
						}
					}
					offset(r = (Effective_Shell_Gap_For_J1 + Effective_Shell_Thickness_For_J1)) {
						union() {
							courtyard_J1();
						}
					}
				}
			}
		}
	}
}
module fitting_cuts_C1_0(){
	union() {
		translate(v = [75.0, -58.04, ((PCB_Thickness - tiny_dimension) + max(4.015739924907685, Effective_Shell_Clearance_From_PCB_For_C1))]) {
			rotate(a = [0, 0, 90.0]) {
				linear_extrude(height = ((min(((topmost_z + c_Base_Thickness) - c_Base_Line_Height), 4.516119992733001) - max(4.015739924907685, Effective_Shell_Clearance_From_PCB_For_C1)) + (2 * tiny_dimension))) {
					union() {
						peri_line_scad([2.634451476740691, -1.3732582236135895],[2.540126091676293, -1.5496178610946558],0.4);
						hull() {
							union() {
								peri_line_scad([12.300734192750506, -1.3681857783096656],[12.397862698924062, -1.5430172780129323],0.4);
								peri_line_scad([12.493334668543685, -1.0588017534356393],[12.678476536588915, -1.134448886208287],0.4);
							}
						}
						hull() {
							union() {
								peri_line_scad([12.493334668543685, -1.0588017534356393],[12.678476536588915, -1.134448886208287],0.4);
								peri_line_scad([12.498348385522492, -1.0361908236945274],[12.696673218890057, -1.0620222090566676],0.4);
							}
						}
						peri_line_scad([12.498348385522492, -1.0361908236945274],[12.696673218890057, -1.0620222090566676],0.4);
						hull() {
							union() {
								peri_line_scad([12.498357433969447, 1.0361341178905477],[12.694872577945995, 1.0733066640486602],0.4);
								peri_line_scad([12.386930854402019, 1.358139088374753],[12.516686335082035, 1.5103347362543755],0.4);
							}
						}
						peri_line_scad([12.386930854402019, 1.358139088374753],[12.516686335082035, 1.5103347362543755],0.4);
						hull() {
							union() {
								peri_line_scad([2.634451476740691, 1.3732582236135895],[2.540126091676293, 1.5496178610946556],0.4);
								peri_line_scad([2.5434434811158164, 1.2365510929360666],[2.362770996813607, 1.3223266921241101],0.4);
							}
						}
						peri_line_scad([2.5434434811158164, 1.2365510929360666],[2.362770996813607, 1.3223266921241101],0.4);
						hull() {
							union() {
								peri_line_scad([2.5434434811158164, -1.2365510929360666],[2.362770996813607, -1.3223266921241101],0.4);
								peri_line_scad([2.634451476740691, -1.3732582236135895],[2.540126091676293, -1.5496178610946558],0.4);
							}
						}
					}
				}
			}
		}
		translate(v = [75.0, -58.04, (PCB_Thickness - tiny_dimension)]) {
			rotate(a = [0, 0, 90.0]) {
				linear_extrude(height = (min(((topmost_z + c_Base_Thickness) - c_Base_Line_Height), 4.516119992733001) + (2 * tiny_dimension))) {
					union() {
						hull() {
							union() {
								peri_line_scad([5.633979961092906, -1.3715635372446675],[(5.633979961092906 + (((0.8800000000000006 + Effective_Shell_Thickness_For_C1) + Effective_Shell_Gap_For_C1) * -0.0005254948981333524)), (-1.3715635372446675 + (((0.8800000000000006 + Effective_Shell_Thickness_For_C1) + Effective_Shell_Gap_For_C1) * -0.9999998619275464))],0.4);
								peri_line_scad([9.30122077499363, -1.3696364206406544],[(9.30122077499363 + (((0.8900000000000006 + Effective_Shell_Thickness_For_C1) + Effective_Shell_Gap_For_C1) * -0.0005254948981333524)), (-1.3696364206406544 + (((0.8900000000000006 + Effective_Shell_Thickness_For_C1) + Effective_Shell_Gap_For_C1) * -0.9999998619275464))],0.4);
							}
						}
						hull() {
							union() {
								peri_line_scad([9.388322390099038, 1.3695906491799776],[(9.388322390099038 + (((0.8900000000000006 + Effective_Shell_Thickness_For_C1) + Effective_Shell_Gap_For_C1) * -0.0005254948981333524)), (1.3695906491799776 + (((0.8900000000000006 + Effective_Shell_Thickness_For_C1) + Effective_Shell_Gap_For_C1) * 0.9999998619275464))],0.4);
								peri_line_scad([5.633979961092906, 1.3715635372446675],[(5.633979961092906 + (((0.8800000000000006 + Effective_Shell_Thickness_For_C1) + Effective_Shell_Gap_For_C1) * -0.0005254948981333524)), (1.3715635372446675 + (((0.8800000000000006 + Effective_Shell_Thickness_For_C1) + Effective_Shell_Gap_For_C1) * 0.9999998619275464))],0.4);
							}
						}
					}
				}
			}
		}
		translate(v = [75.0, -58.04, ((PCB_Thickness - tiny_dimension) + max(3.512820041179657, Effective_Shell_Clearance_From_PCB_For_C1))]) {
			rotate(a = [0, 0, 90.0]) {
				linear_extrude(height = ((min(((topmost_z + c_Base_Thickness) - c_Base_Line_Height), 4.015739924907685) - max(3.512820041179657, Effective_Shell_Clearance_From_PCB_For_C1)) + (2 * tiny_dimension))) {
					union() {
						hull() {
							union() {
								peri_line_scad([2.6544913674514494, 1.8151184361792123],[2.6161960761667054, 2.011417877506529],0.4);
								peri_line_scad([2.5762169088215487, 1.7848659242712441],[2.4448646969715604, 1.9356856724546827],0.4);
							}
						}
						hull() {
							union() {
								peri_line_scad([2.5762169088215487, 1.7848659242712441],[2.4448646969715604, 1.9356856724546827],0.4);
								peri_line_scad([2.513011389585744, 1.6710118148084074],[2.322744857400925, 1.7326449773944963],0.4);
							}
						}
						peri_line_scad([2.513011389585744, 1.6710118148084074],[2.322744857400925, 1.7326449773944963],0.4);
						hull() {
							union() {
								peri_line_scad([2.513011389585744, -1.6710118148084074],[2.322744857400925, -1.7326449773944963],0.4);
								peri_line_scad([2.5762169088215487, -1.7848659242712441],[2.4448646969715604, -1.9356856724546827],0.4);
							}
						}
						hull() {
							union() {
								peri_line_scad([2.5762169088215487, -1.7848659242712441],[2.4448646969715604, -1.9356856724546827],0.4);
								peri_line_scad([2.6544887221315583, -1.8151179238126391],[2.6167224948250163, -2.0115198384546065],0.4);
							}
						}
						peri_line_scad([2.6544887221315583, -1.8151179238126391],[2.6167224948250163, -2.0115198384546065],0.4);
						hull() {
							union() {
								peri_line_scad([12.344256671972161, -1.815110307320742],[12.372990102857235, -2.0130355203421573],0.4);
								peri_line_scad([12.42514450934624, -1.784775801538217],[12.53234340914116, -1.9536200963271102],0.4);
							}
						}
						hull() {
							union() {
								peri_line_scad([12.42514450934624, -1.784775801538217],[12.53234340914116, -1.9536200963271102],0.4);
								peri_line_scad([12.455288725063927, -1.759728375767074],[12.629444881101751, -1.8580626694500455],0.4);
							}
						}
						peri_line_scad([12.455288725063927, -1.759728375767074],[12.629444881101751, -1.8580626694500455],0.4);
						hull() {
							union() {
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
